venice1200/MiSTer_tty2oled/PCBs_and_Cases/tty2oled_esp32-DevKitC_board.png

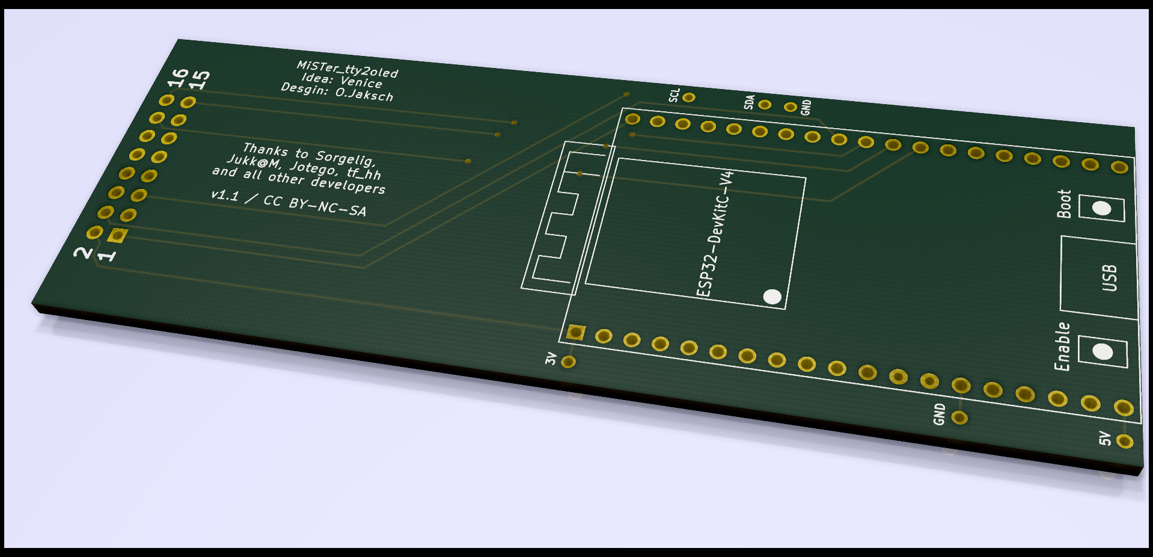
PCBs_and_Cases/tty2oled_esp32-DevKitC_board.png
