venice1200/MiSTer_tty2oled/PCBs_and_Cases/tty2oled_esp32-ttgo-t8-v1.7.1_board.png

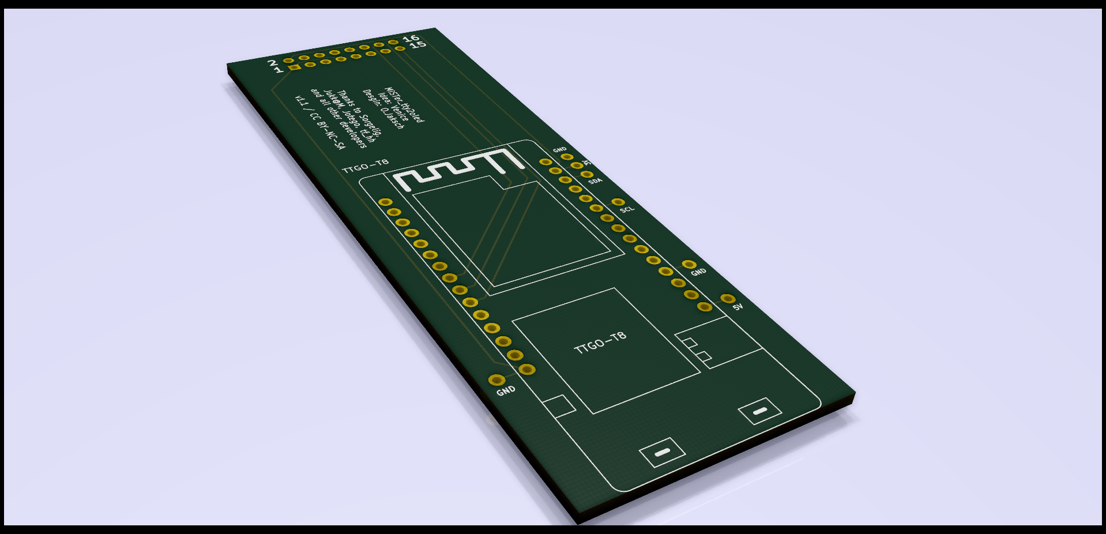
PCBs_and_Cases/tty2oled_esp32-ttgo-t8-v1.7.1_board.png
