venice1200/MiSTer_tty2oled/PCBs_and_Cases/tty2oled_esp8266-NodeMCU_v3_board.png

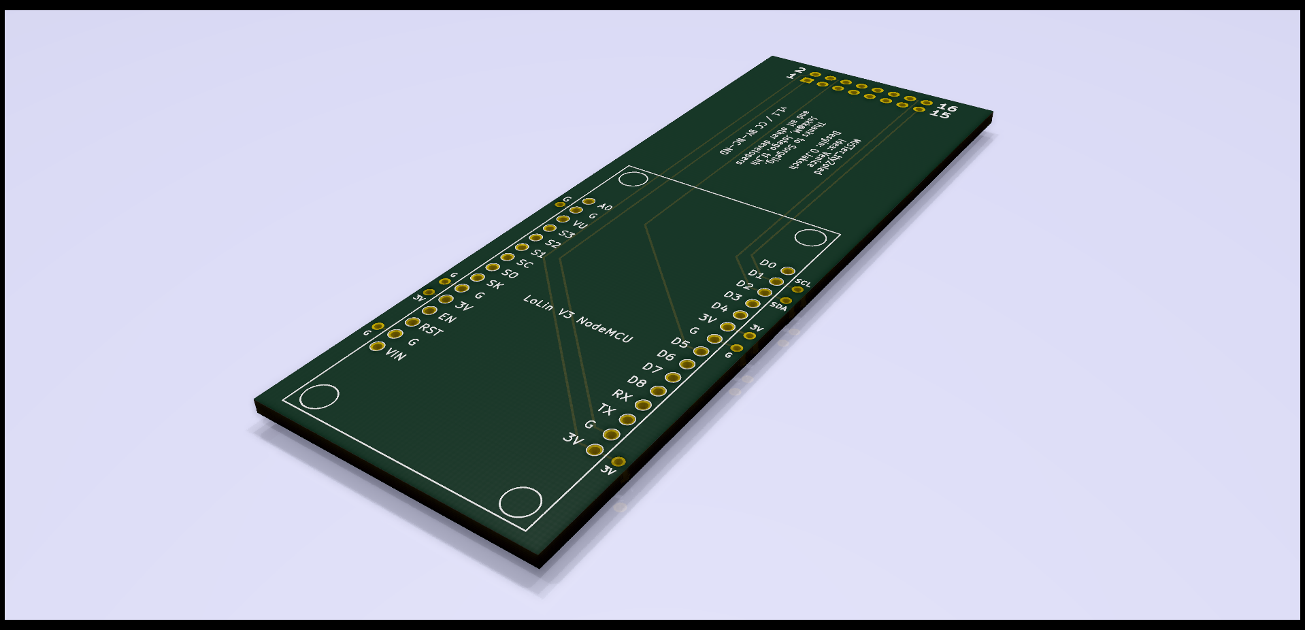
PCBs_and_Cases/tty2oled_esp8266-NodeMCU_v3_board.png
