venice1200/MiSTer_tty2oled/Pictures/altbeast55.jpg

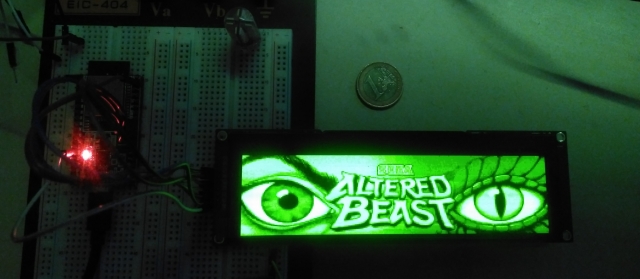
Pictures/altbeast55.jpg
