venice1200/MiSTer_tty2oled/Pictures/Arduino_1.8.13_ESP8266-NodeMCU_v3_Settings.png

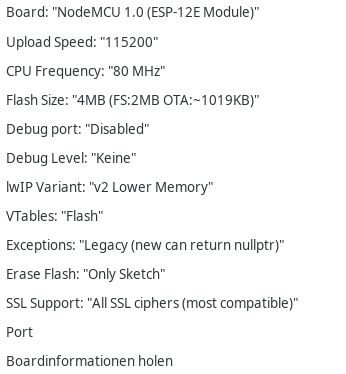
Pictures/Arduino_1.8.13_ESP8266-NodeMCU_v3_Settings.png
