venice1200/MiSTer_tty2oled/Pictures/Arduino_1.8.13_Lolin32_Settings.jpg

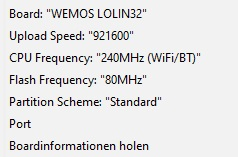
Pictures/Arduino_1.8.13_Lolin32_Settings.jpg
