venice1200/MiSTer_tty2oled/Pictures/Arduino_1.8.13_TTGO-T8_v1.7.1_Settings.jpg

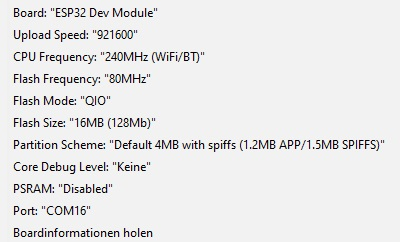
Pictures/Arduino_1.8.13_TTGO-T8_v1.7.1_Settings.jpg
