venice1200/MiSTer_tty2oled/Pictures/BasicOTA_small.jpg

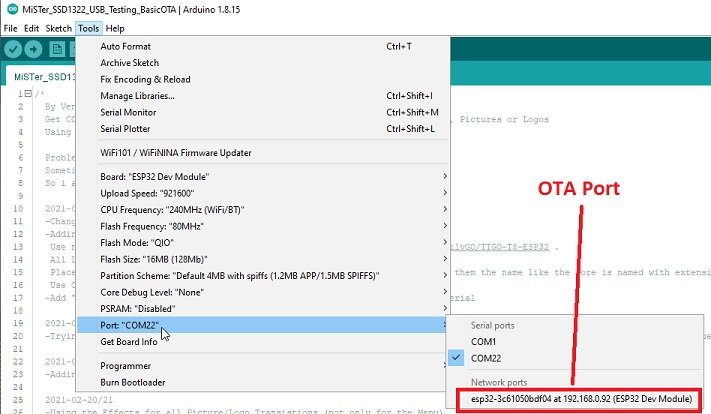
Pictures/BasicOTA_small.jpg
