venice1200/MiSTer_tty2oled/Pictures/Case_with_OLED_small.jpg

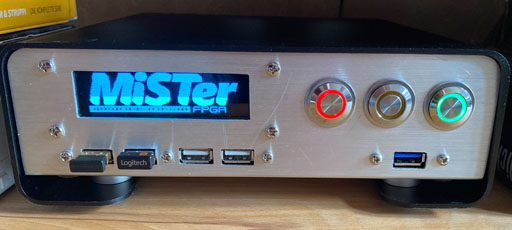
Pictures/Case_with_OLED_small.jpg
