venice1200/MiSTer_tty2oled/Pictures/Connection_Scheme_DevKitC_v4-SSD1322.jpg

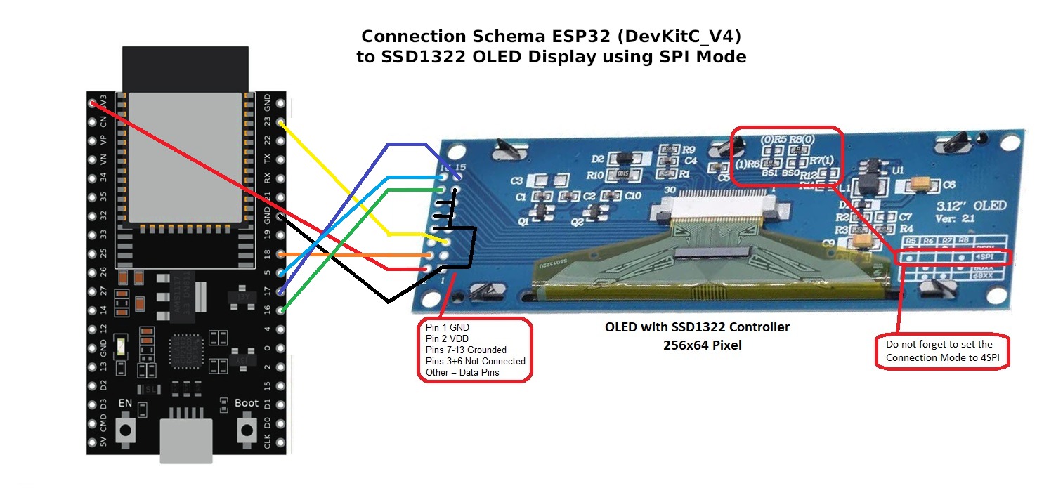
Pictures/Connection_Scheme_DevKitC_v4-SSD1322.jpg
