venice1200/MiSTer_tty2oled/Pictures/Connection_Scheme_NodeMCU-SSD1322.jpg

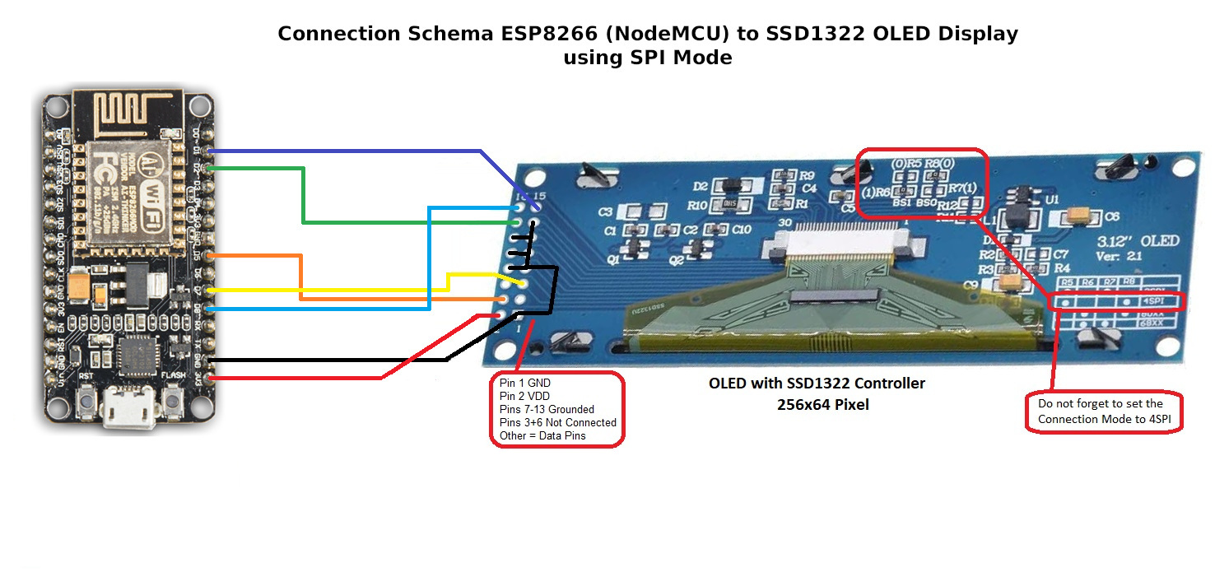
Pictures/Connection_Scheme_NodeMCU-SSD1322.jpg
