venice1200/MiSTer_tty2oled/Pictures/Connection_Scheme_NodeMCU-SSD1322_NewHaven_Displays.jpg.png

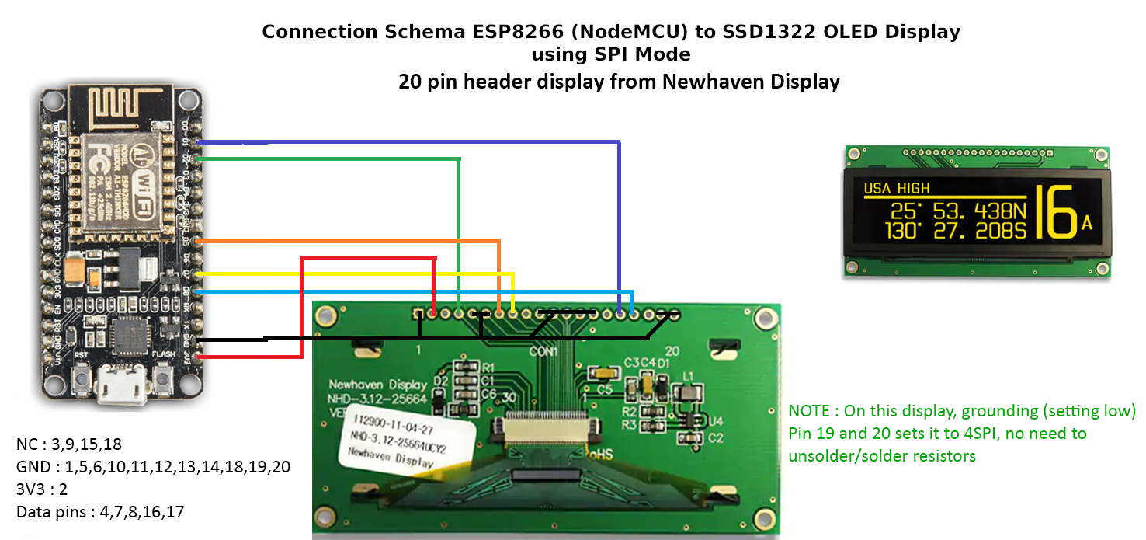
Pictures/Connection_Scheme_NodeMCU-SSD1322_NewHaven_Displays.jpg.png
