venice1200/MiSTer_tty2oled/Pictures/Connection_Scheme_TTGO-SSD1322.jpg

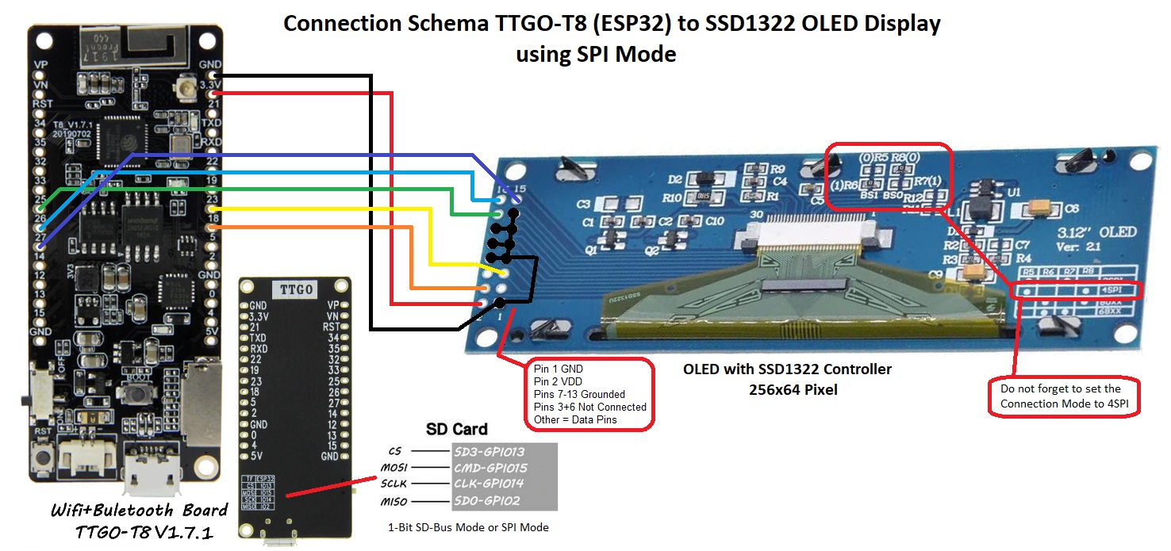
Pictures/Connection_Scheme_TTGO-SSD1322.jpg
