venice1200/MiSTer_tty2oled/Pictures/d.ti_rev1.2_small.jpg

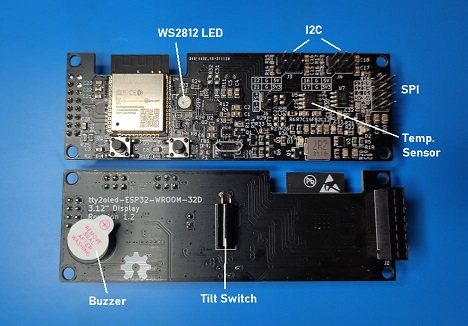
Pictures/d.ti_rev1.2_small.jpg
