venice1200/MiSTer_tty2oled/Pictures/d.ti_small.jpg

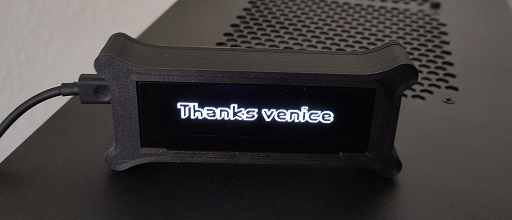
Pictures/d.ti_small.jpg
