venice1200/MiSTer_tty2oled/Pictures/d.ti_small_tty2oled_wroom_32d.jpg

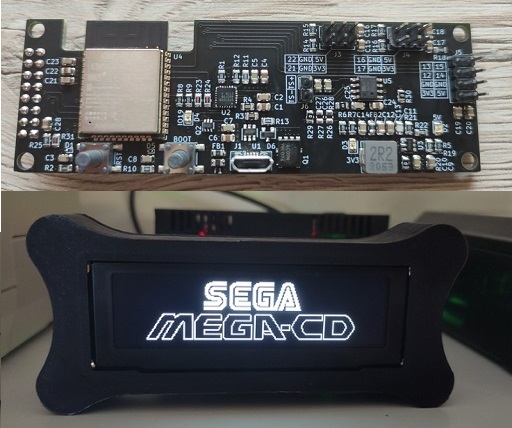
Pictures/d.ti_small_tty2oled_wroom_32d.jpg
