venice1200/MiSTer_tty2oled/Pictures/dave18_small.jpg

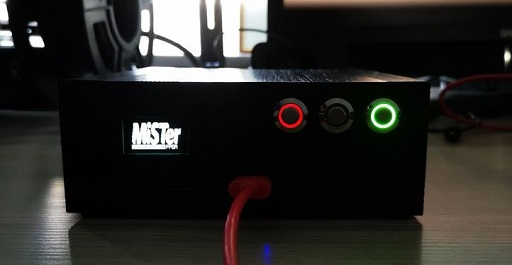
Pictures/dave18_small.jpg
