venice1200/MiSTer_tty2oled/Pictures/ExtCase312_small.jpg

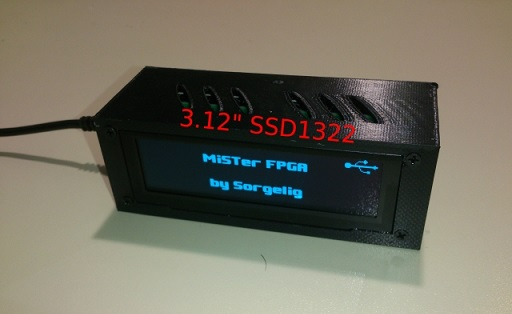
Pictures/ExtCase312_small.jpg
