venice1200/MiSTer_tty2oled/Pictures/gojira54_small.jpg

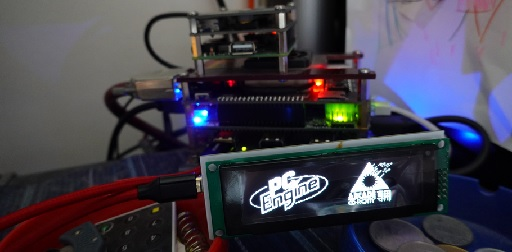
Pictures/gojira54_small.jpg
