venice1200/MiSTer_tty2oled/Pictures/jawler_small.jpg

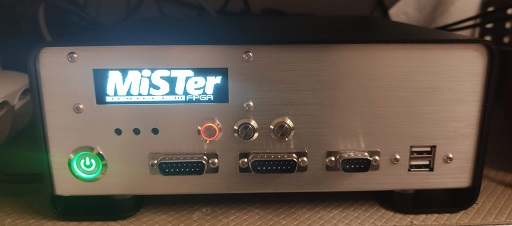
Pictures/jawler_small.jpg
