venice1200/MiSTer_tty2oled/Pictures/Jukk_at_M_small.jpg

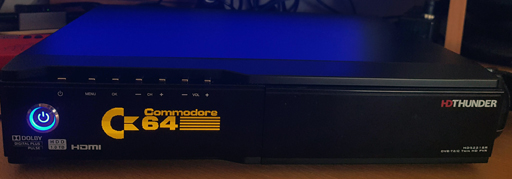
Pictures/Jukk_at_M_small.jpg
