venice1200/MiSTer_tty2oled/Pictures/Lolin_PCB_BOT_small.jpg

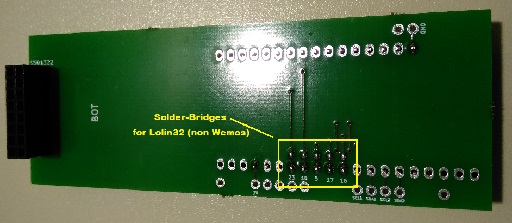
Pictures/Lolin_PCB_BOT_small.jpg
