venice1200/MiSTer_tty2oled/Pictures/Mellified_small.jpg

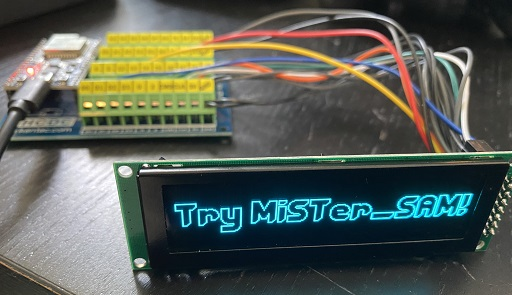
Pictures/Mellified_small.jpg
