venice1200/MiSTer_tty2oled/Pictures/OLED_Connection.jpg

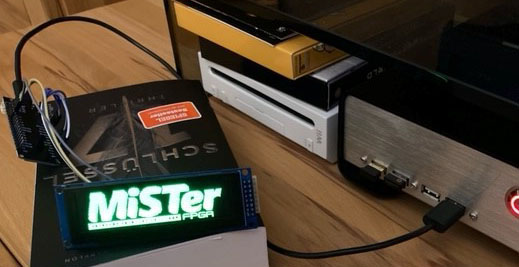
Pictures/OLED_Connection.jpg
