venice1200/MiSTer_tty2oled/Pictures/Prototype_small.jpg

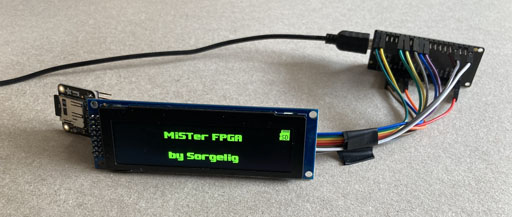
Pictures/Prototype_small.jpg
