venice1200/MiSTer_tty2oled/Pictures/rbz_couchcase_small.jpg

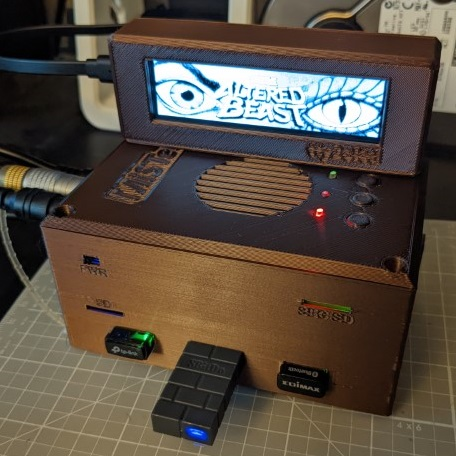
Pictures/rbz_couchcase_small.jpg
