venice1200/MiSTer_tty2oled/Pictures/Reg_small.JPG

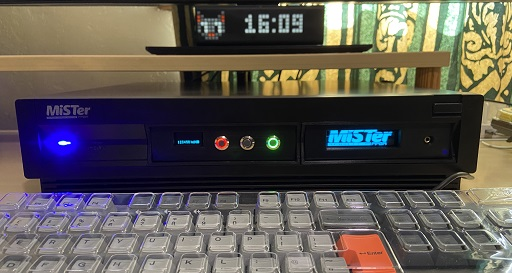
Pictures/Reg_small.JPG
