venice1200/MiSTer_tty2oled/Pictures/SerialMonitor_1.png

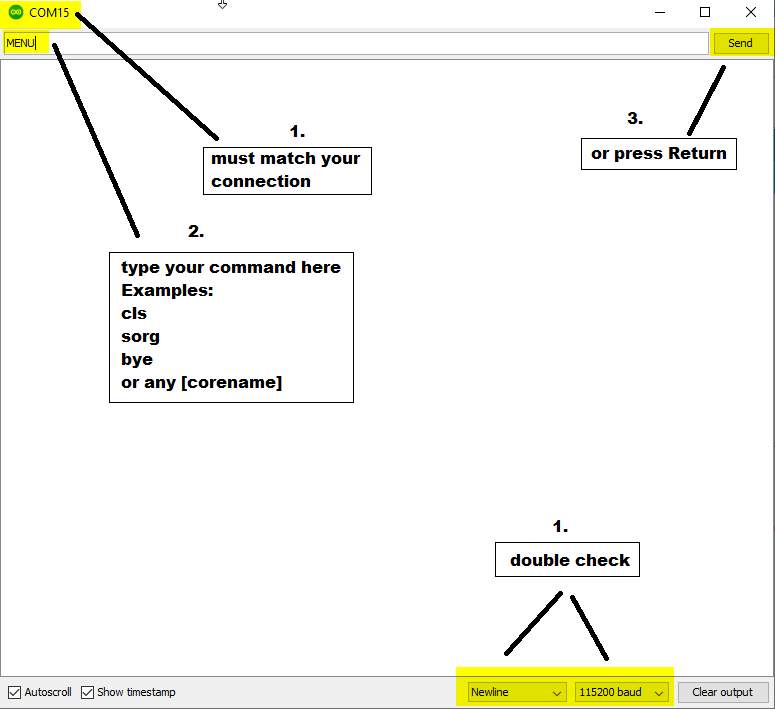
Pictures/SerialMonitor_1.png
