venice1200/MiSTer_tty2oled/Pictures/SerialMonitor_1_small.png

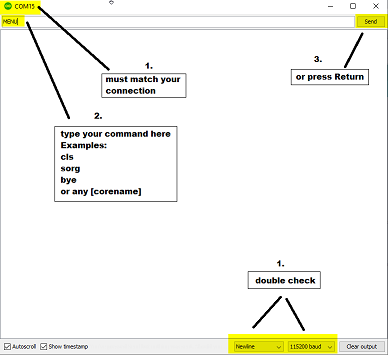
Pictures/SerialMonitor_1_small.png
