venice1200/MiSTer_tty2oled/Pictures/SerialMonitor_Open.png

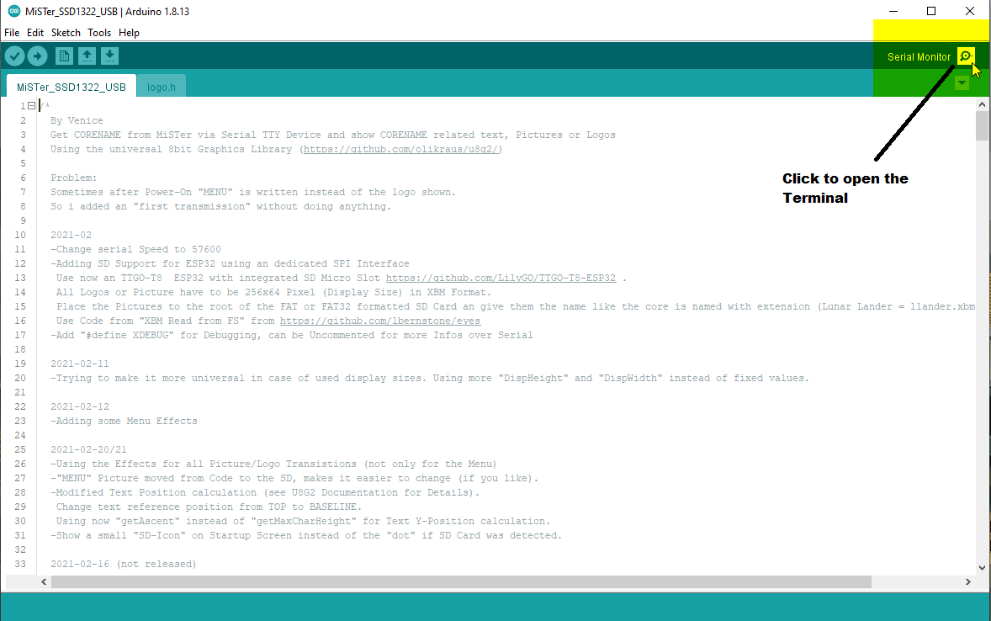
Pictures/SerialMonitor_Open.png
