venice1200/MiSTer_tty2oled/Pictures/stefer09-2_small.jpg

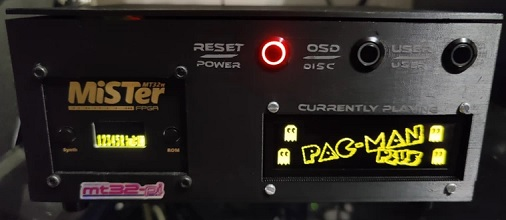
Pictures/stefer09-2_small.jpg
