venice1200/MiSTer_tty2oled/Pictures/stefer09_small.jpg

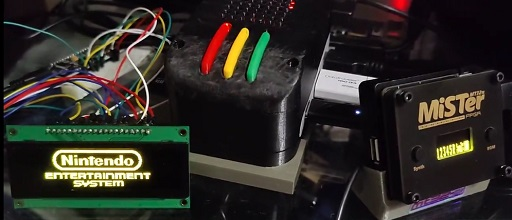
Pictures/stefer09_small.jpg
