venice1200/MiSTer_tty2oled/Pictures/ThreeColor_small.jpeg

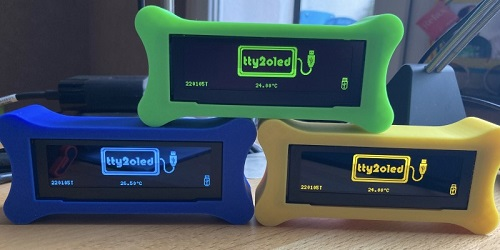
Pictures/ThreeColor_small.jpeg
