venice1200/MiSTer_tty2oled/Pictures/WiteWulf_small.jpg

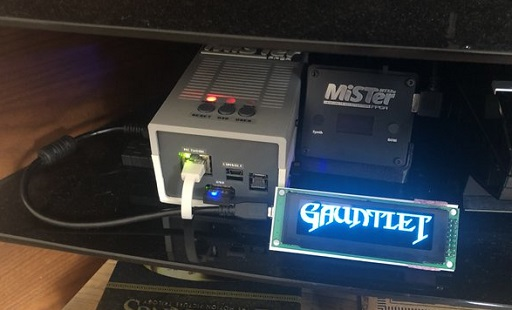
Pictures/WiteWulf_small.jpg
