venice1200/MiSTer_tty2oled/Pictures/With_OLED_Top_Small.jpg

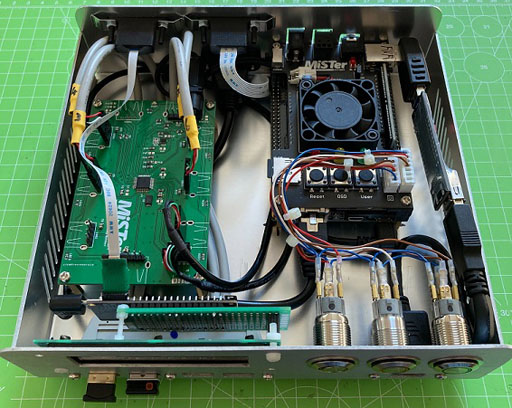
Pictures/With_OLED_Top_Small.jpg
