venice1200/MiSTer_tty2oled/Pictures/HowTo/tty2oled_arduino_01_folders.png

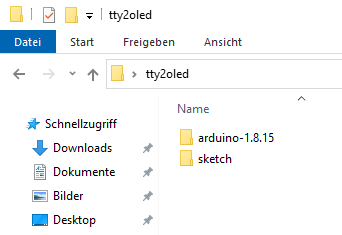
Pictures/HowTo/tty2oled_arduino_01_folders.png
