venice1200/MiSTer_tty2oled/Pictures/HowTo/tty2oled_arduino_02_preferences.png

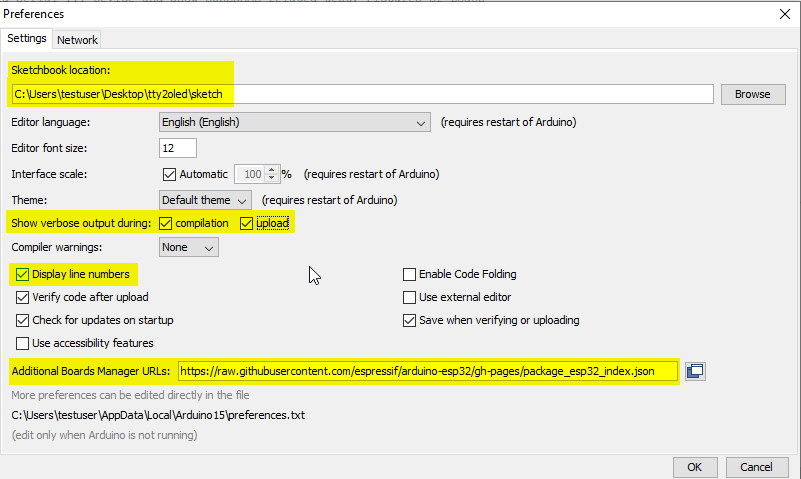
Pictures/HowTo/tty2oled_arduino_02_preferences.png
