venice1200/MiSTer_tty2oled/Pictures/HowTo/tty2oled_arduino_03_board_01_menu.png

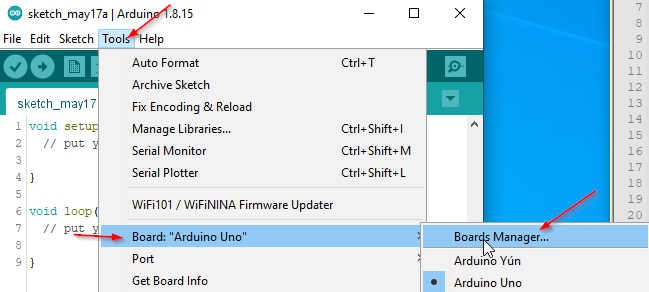
Pictures/HowTo/tty2oled_arduino_03_board_01_menu.png
