venice1200/MiSTer_tty2oled/Pictures/HowTo/tty2oled_arduino_04_library_02_u8g2.png

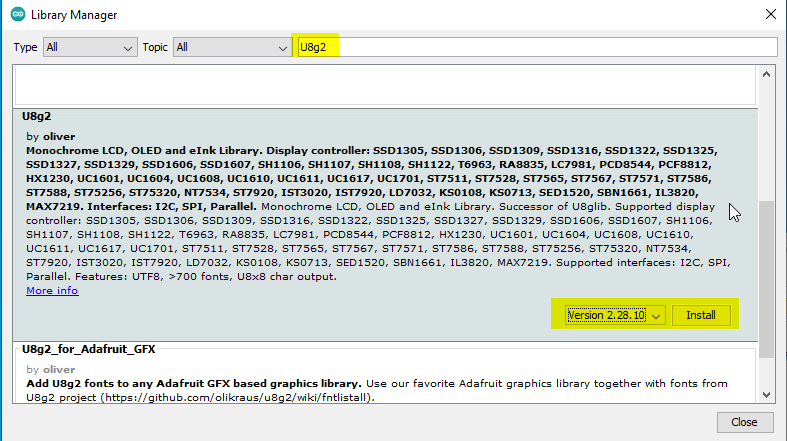
Pictures/HowTo/tty2oled_arduino_04_library_02_u8g2.png
