venice1200/MiSTer_tty2oled/Pictures/HowTo/tty2oled_arduino_06_sketch_01_open.png

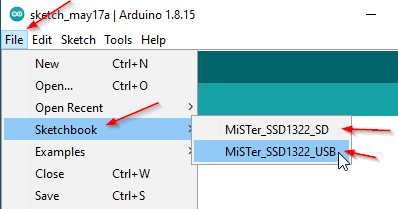
Pictures/HowTo/tty2oled_arduino_06_sketch_01_open.png
