venice1200/MiSTer_tty2oled/Pictures/HowTo/tty2oled_arduino_06_sketch_02_opened.png

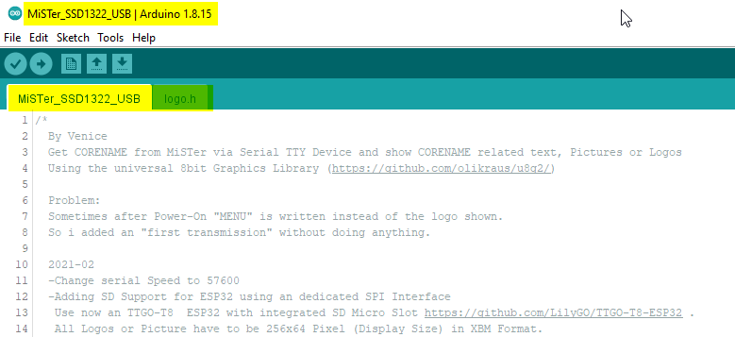
Pictures/HowTo/tty2oled_arduino_06_sketch_02_opened.png
