venice1200/MiSTer_tty2oled/Pictures/HowTo/tty2oled_arduino_08_sketch_01_choose_ESP.png

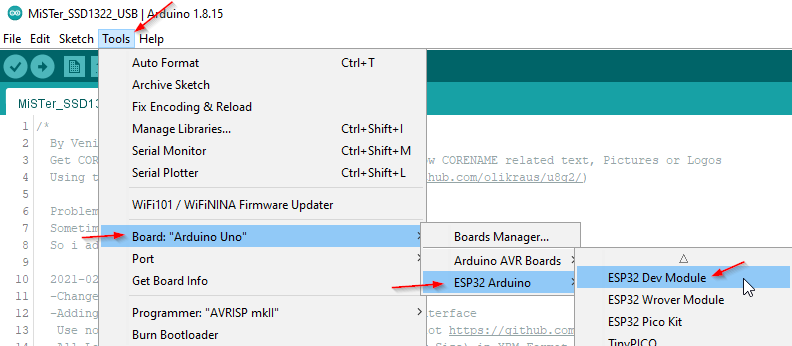
Pictures/HowTo/tty2oled_arduino_08_sketch_01_choose_ESP.png
