venice1200/MiSTer_tty2oled/Pictures/HowTo/tty2oled_arduino_08_sketch_02_check_ESP.png

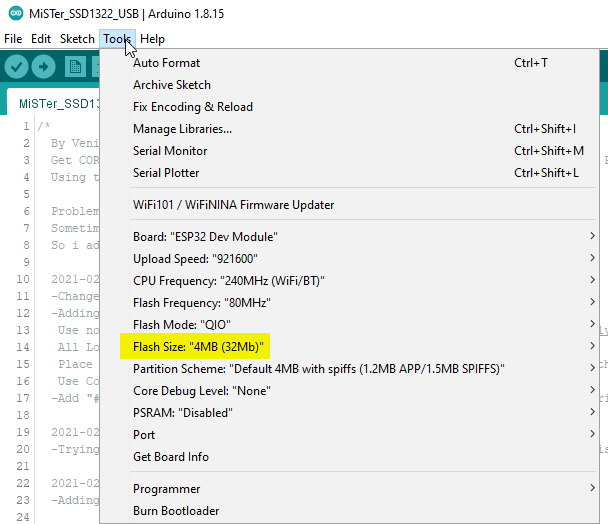
Pictures/HowTo/tty2oled_arduino_08_sketch_02_check_ESP.png
