venice1200/MiSTer_tty2oled/Pictures/HowTo/tty2oled_arduino_09_sketch_02_compiling.png

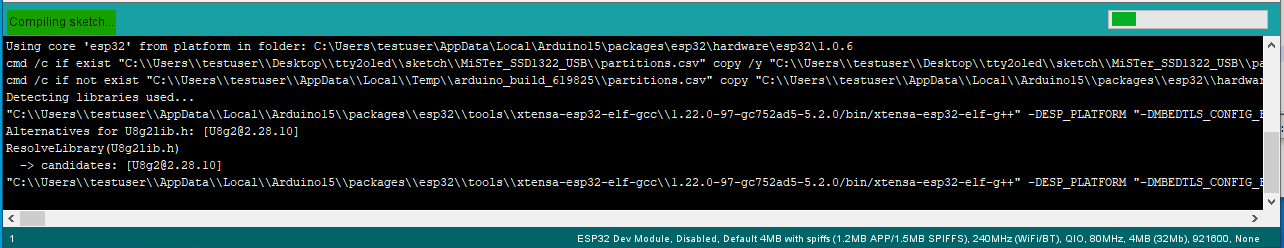
Pictures/HowTo/tty2oled_arduino_09_sketch_02_compiling.png
