venice1200/MiSTer_tty2oled/Pictures/HowTo/tty2oled_arduino_09_sketch_03_compiled.png

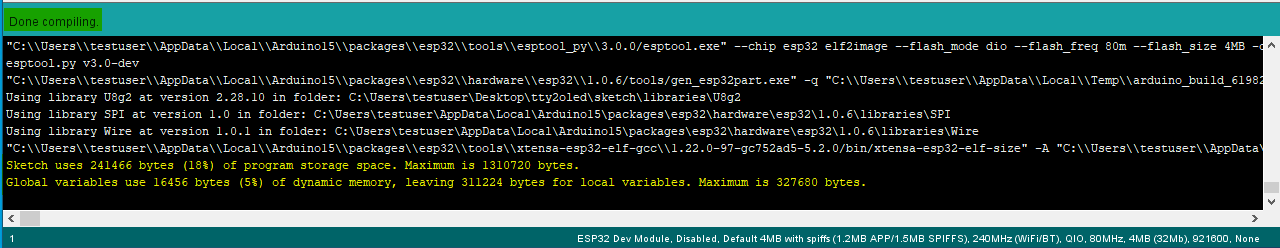
Pictures/HowTo/tty2oled_arduino_09_sketch_03_compiled.png
