venice1200/MiSTer_tty2oled/Pictures/HowTo/tty2oled_arduino_10_windows_02_driver.png

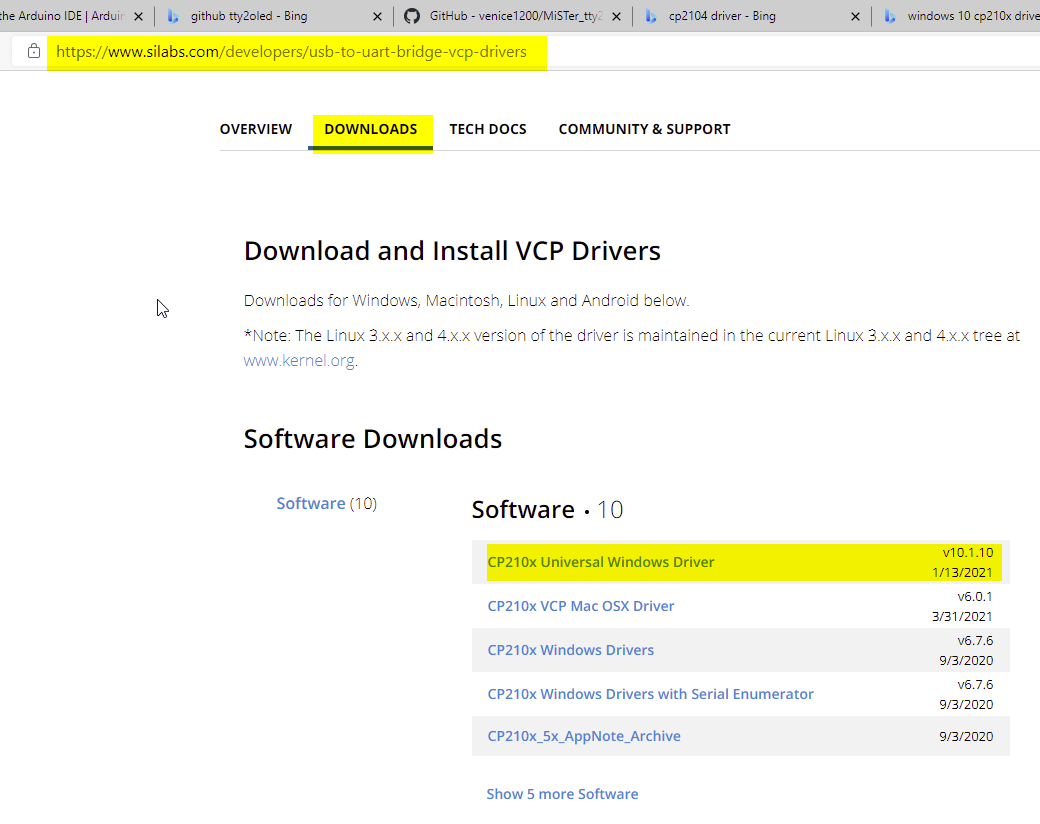
Pictures/HowTo/tty2oled_arduino_10_windows_02_driver.png
