venice1200/MiSTer_tty2oled/Pictures/HowTo/tty2oled_arduino_11_sketch_01_port.png

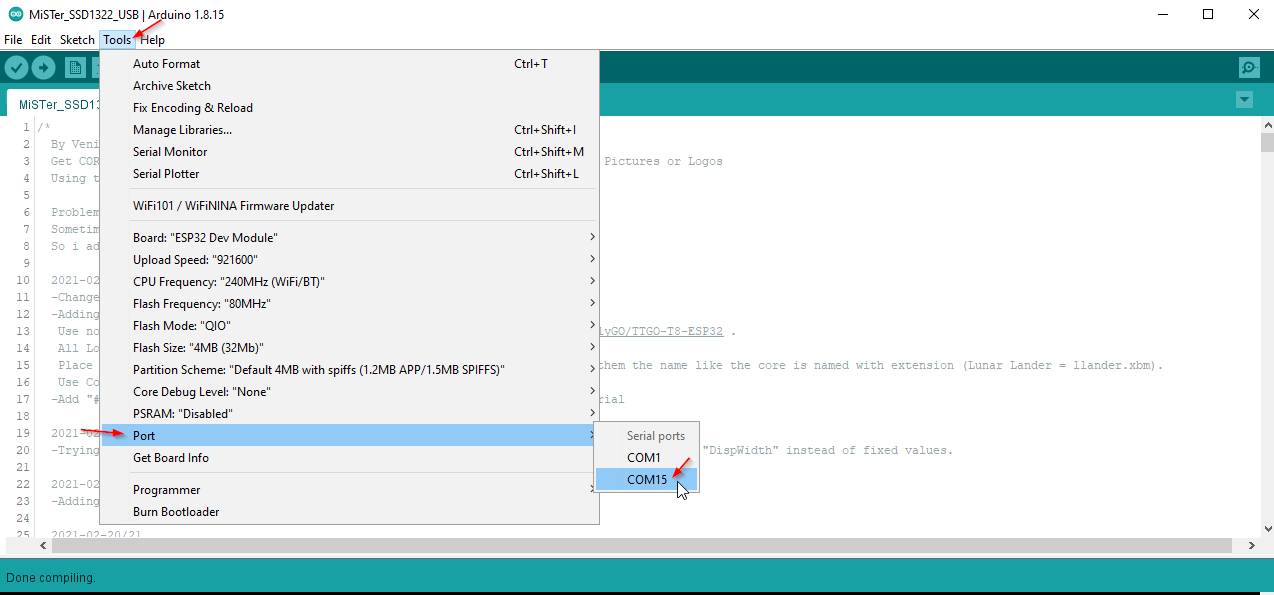
Pictures/HowTo/tty2oled_arduino_11_sketch_01_port.png
