venice1200/MiSTer_tty2oled/Pictures/HowTo/tty2oled_arduino_12_sketch_01_upload.png

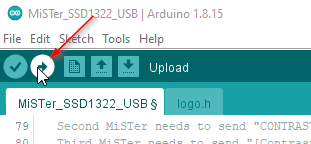
Pictures/HowTo/tty2oled_arduino_12_sketch_01_upload.png
