venice1200/MiSTer_tty2oled/Pictures/HowTo/tty2oled_arduino_12_sketch_02_uploading.png

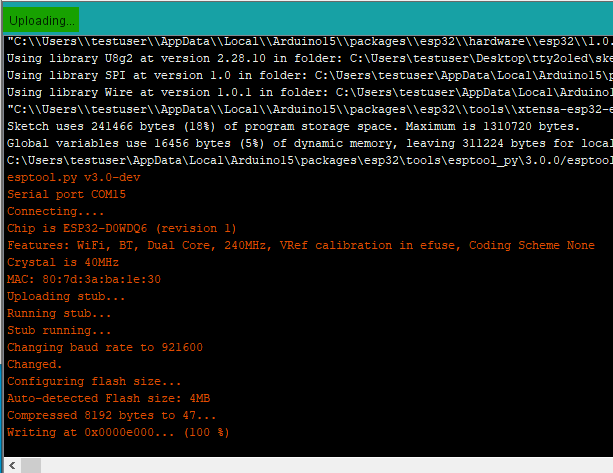
Pictures/HowTo/tty2oled_arduino_12_sketch_02_uploading.png
