venice1200/MiSTer_tty2oled/Pictures/HowTo/tty2oled_arduino_14_BasicOTA_06.jpg

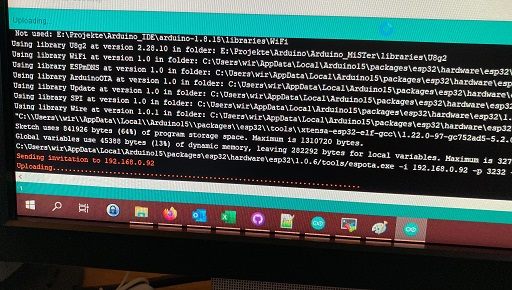
Pictures/HowTo/tty2oled_arduino_14_BasicOTA_06.jpg
