venice1200/MiSTer_tty2oled/Pictures/312_v21_measured.jpg

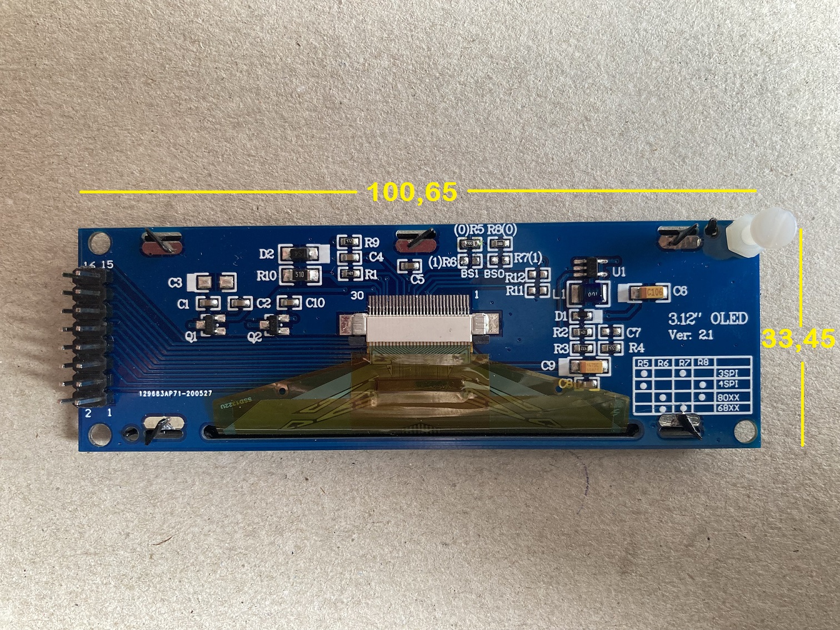
Pictures/312_v21_measured.jpg
