venice1200/MiSTer_tty2oled/MiSTer_SSD1322_USB/logo.h

/*
  Logo's for MiSTer in XMB Format
  Most of them defined as "static const unsigned char <Name>[]U8X8_PROGMEM" for the useage of "u8g2.drawXBMP"
  only the mister logo is defined as "static unsigned char <Name>[]" because the effects must use "u8g2.drawXBM".
*/

/* Menu Picture moved to SD */

/* -------------------- U8X8_PROGMEM -----------------------*/

// SD Logo 16x16
#define sdcard_icon16_width 16
#define sdcard_icon16_height 16
const uint8_t PROGMEM sdcard_icon16[] = {
 0x50,0x55,0x58,0x55,0x58,0x55,0x58,0x55,0xf8,0x7f,0xfc,0x7f,0xfe,0x7f,0xfe,
 0x7f,0x1e,0x71,0xec,0x6d,0xec,0x6d,0x9e,0x6d,0x7e,0x6d,0x7e,0x6d,0x8e,0x71,
 0xfe,0x7f };

#define usb_icon_width 9
#define usb_icon_height 18
const uint8_t PROGMEM usb_icon[] = {
 0xfe,0x00,0x82,0x00,0xaa,0x00,0xaa,0x00,0x82,0x00,0xff,0x01,
 0x01,0x01,0x11,0x01,0x51,0x01,0x55,0x01,0x35,0x01,0x19,0x01,
 0x11,0x01,0x11,0x01,0x01,0x01,0x39,0x01,0x82,0x00,0x7c,0x00};

// Sorgelig's Icon 16x16
#define sorgelig_icon16_width 16
#define sorgelig_icon16_height 16
const uint8_t PROGMEM sorgelig_icon16[] = {
 0x38,0x1c,0x38,0x1c,0xfc,0x3f,0xfe,0x7f,0x06,0x60,0xc6,0x61,0xfe,0x7f,0xfe,
 0x7f,0xdf,0xfb,0xfb,0xdf,0xe3,0xc7,0x26,0x64,0x06,0x60,0x86,0x61,0xc2,0xc3,
 0x7e,0x7f };
 
// MiSTer Logo for Screensaver
#define mister_logo32_width 116
#define mister_logo32_height 32
const uint8_t PROGMEM mister_logo32[] = {
   0x00, 0x00, 0x00, 0x00, 0xc0, 0x1f, 0xe0, 0x1f, 0x00, 0x00, 0x00, 0x00,
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
 0x00,0x00,0x00,0x00,0x00,0x00,0x00,0x00,0x00,0x00,0x00,0x00,
 0x55,0x55,0x55,0x55,0x00,0x00,0x00,0x10,0x00,0x00,0x00,0x00,
 0x00,0x00,0x00,0x00,0x00,0x00,0x00,0x00,0x00,0x00,0x00,0x00,
 0x00,0x00,0x00,0x00,0x00,0x00,0x00,0x00,0xAB,0xAA,0xAA,0xAA,
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
