venice1200/MiSTer_tty2oled/Testing/docs_and_obsoletes/esptool.py

#!/usr/bin/python3
#
# ESP8266 & ESP32 family & ESP8684 ROM Bootloader Utility
# Copyright (C) 2014-2021 Fredrik Ahlberg, Angus Gratton, Espressif Systems (Shanghai) CO LTD, other contributors as noted.
# https://github.com/espressif/esptool
#
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
from __future__ import division, print_function

import argparse
import base64
import binascii
import copy
import hashlib
import inspect
import io
import itertools
import os
import re
import shlex
import string
import struct
import sys
import time
import zlib

try:
    import serial
except ImportError:
    print("Pyserial is not installed for %s. Check the README for installation instructions." % (sys.executable))
    raise

# check 'serial' is 'pyserial' and not 'serial' https://github.com/espressif/esptool/issues/269
try:
    if "serialization" in serial.__doc__ and "deserialization" in serial.__doc__:
        raise ImportError("""
esptool.py depends on pyserial, but there is a conflict with a currently installed package named 'serial'.

You may be able to work around this by 'pip uninstall serial; pip install pyserial' \
but this may break other installed Python software that depends on 'serial'.

There is no good fix for this right now, apart from configuring virtualenvs. \
See https://github.com/espressif/esptool/issues/269#issuecomment-385298196 for discussion of the underlying issue(s).""")
except TypeError:
    pass  # __doc__ returns None for pyserial

try:
    import serial.tools.list_ports as list_ports
except ImportError:
    print("The installed version (%s) of pyserial appears to be too old for esptool.py (Python interpreter %s). "
          "Check the README for installation instructions." % (sys.VERSION, sys.executable))
    raise
except Exception:
    if sys.platform == "darwin":
        # swallow the exception, this is a known issue in pyserial+macOS Big Sur preview ref https://github.com/espressif/esptool/issues/540
        list_ports = None
    else:
        raise


__version__ = "3.2"

MAX_UINT32 = 0xffffffff
MAX_UINT24 = 0xffffff

DEFAULT_TIMEOUT = 3                   # timeout for most flash operations
START_FLASH_TIMEOUT = 20              # timeout for starting flash (may perform erase)
CHIP_ERASE_TIMEOUT = 120              # timeout for full chip erase
MAX_TIMEOUT = CHIP_ERASE_TIMEOUT * 2  # longest any command can run
SYNC_TIMEOUT = 0.1                    # timeout for syncing with bootloader
MD5_TIMEOUT_PER_MB = 8                # timeout (per megabyte) for calculating md5sum
ERASE_REGION_TIMEOUT_PER_MB = 30      # timeout (per megabyte) for erasing a region
ERASE_WRITE_TIMEOUT_PER_MB = 40       # timeout (per megabyte) for erasing and writing data
MEM_END_ROM_TIMEOUT = 0.05            # special short timeout for ESP_MEM_END, as it may never respond
DEFAULT_SERIAL_WRITE_TIMEOUT = 10     # timeout for serial port write
DEFAULT_CONNECT_ATTEMPTS = 7          # default number of times to try connection

SUPPORTED_CHIPS = ['esp8266', 'esp32', 'esp32s2', 'esp32s3beta2', 'esp32s3', 'esp32c3', 'esp32c6beta', 'esp32h2', 'esp8684']


def timeout_per_mb(seconds_per_mb, size_bytes):
    """ Scales timeouts which are size-specific """
    result = seconds_per_mb * (size_bytes / 1e6)
    if result < DEFAULT_TIMEOUT:
        return DEFAULT_TIMEOUT
    return result


def _chip_to_rom_loader(chip):
    return {
        'esp8266': ESP8266ROM,
        'esp32': ESP32ROM,
        'esp32s2': ESP32S2ROM,
        'esp32s3beta2': ESP32S3BETA2ROM,
        'esp32s3': ESP32S3ROM,
        'esp32c3': ESP32C3ROM,
        'esp32c6beta': ESP32C6BETAROM,
        'esp32h2': ESP32H2ROM,
        'esp8684': ESP8684ROM,
    }[chip]


def get_default_connected_device(serial_list, port, connect_attempts, initial_baud, chip='auto', trace=False,
                                 before='default_reset'):
    _esp = None
    for each_port in reversed(serial_list):
        print("Serial port %s" % each_port)
        try:
            if chip == 'auto':
                _esp = ESPLoader.detect_chip(each_port, initial_baud, before, trace,
                                             connect_attempts)
            else:
                chip_class = _chip_to_rom_loader(chip)
                _esp = chip_class(each_port, initial_baud, trace)
                _esp.connect(before, connect_attempts)
            break
        except (FatalError, OSError) as err:
            if port is not None:
                raise
            print("%s failed to connect: %s" % (each_port, err))
            _esp = None
    return _esp


DETECTED_FLASH_SIZES = {0x12: '256KB', 0x13: '512KB', 0x14: '1MB',
                        0x15: '2MB', 0x16: '4MB', 0x17: '8MB',
                        0x18: '16MB', 0x19: '32MB', 0x1a: '64MB'}


def check_supported_function(func, check_func):
    """
    Decorator implementation that wraps a check around an ESPLoader
    bootloader function to check if it's supported.

    This is used to capture the multidimensional differences in
    functionality between the ESP8266 & ESP32/32S2/32S3/32C3 & ESP8684 ROM loaders, and the
    software stub that runs on both. Not possible to do this cleanly
    via inheritance alone.
    """
    def inner(*args, **kwargs):
        obj = args[0]
        if check_func(obj):
            return func(*args, **kwargs)
        else:
            raise NotImplementedInROMError(obj, func)
    return inner


def stub_function_only(func):
    """ Attribute for a function only supported in the software stub loader """
    return check_supported_function(func, lambda o: o.IS_STUB)


def stub_and_esp32_function_only(func):
    """ Attribute for a function only supported by software stubs or ESP32/32S2/32S3/32C3 ROM """
    return check_supported_function(func, lambda o: o.IS_STUB or isinstance(o, ESP32ROM))


def esp32s3_or_newer_function_only(func):
    """ Attribute for a function only supported by ESP32S3/32C3 & ESP8684 ROM """
    return check_supported_function(func, lambda o: isinstance(o, ESP32S3ROM) or isinstance(o, ESP32C3ROM))


PYTHON2 = sys.version_info[0] < 3  # True if on pre-Python 3

# Function to return nth byte of a bitstring
# Different behaviour on Python 2 vs 3
if PYTHON2:
    def byte(bitstr, index):
        return ord(bitstr[index])
else:
    def byte(bitstr, index):
        return bitstr[index]

# Provide a 'basestring' class on Python 3
try:
    basestring
except NameError:
    basestring = str


def print_overwrite(message, last_line=False):
    """ Print a message, overwriting the currently printed line.

    If last_line is False, don't append a newline at the end (expecting another subsequent call will overwrite this one.)

    After a sequence of calls with last_line=False, call once with last_line=True.

    If output is not a TTY (for example redirected a pipe), no overwriting happens and this function is the same as print().
    """
    if sys.stdout.isatty():
        print("\r%s" % message, end='\n' if last_line else '')
    else:
        print(message)


def _mask_to_shift(mask):
    """ Return the index of the least significant bit in the mask """
    shift = 0
    while mask & 0x1 == 0:
        shift += 1
        mask >>= 1
    return shift


def esp8266_function_only(func):
    """ Attribute for a function only supported on ESP8266 """
    return check_supported_function(func, lambda o: o.CHIP_NAME == "ESP8266")


class ESPLoader(object):
    """ Base class providing access to ESP ROM & software stub bootloaders.
    Subclasses provide ESP8266 & ESP32 Family & ESP8684 specific functionality.

    Don't instantiate this base class directly, either instantiate a subclass or
    call ESPLoader.detect_chip() which will interrogate the chip and return the
    appropriate subclass instance.

    """
    CHIP_NAME = "Espressif device"
    IS_STUB = False

    FPGA_SLOW_BOOT = False

    DEFAULT_PORT = "/dev/ttyUSB0"

    # Commands supported by ESP8266 ROM bootloader
    ESP_FLASH_BEGIN = 0x02
    ESP_FLASH_DATA  = 0x03
    ESP_FLASH_END   = 0x04
    ESP_MEM_BEGIN   = 0x05
    ESP_MEM_END     = 0x06
    ESP_MEM_DATA    = 0x07
    ESP_SYNC        = 0x08
    ESP_WRITE_REG   = 0x09
    ESP_READ_REG    = 0x0a

    # Some comands supported by ESP32 & ESP8684 ROM bootloader (or -8266 w/ stub)
    ESP_SPI_SET_PARAMS = 0x0B
    ESP_SPI_ATTACH     = 0x0D
    ESP_READ_FLASH_SLOW  = 0x0e  # ROM only, much slower than the stub flash read
    ESP_CHANGE_BAUDRATE = 0x0F
    ESP_FLASH_DEFL_BEGIN = 0x10
    ESP_FLASH_DEFL_DATA  = 0x11
    ESP_FLASH_DEFL_END   = 0x12
    ESP_SPI_FLASH_MD5    = 0x13

    # Commands supported by ESP32-S2/S3/C3/C6 & ESP8684 ROM bootloader only
    ESP_GET_SECURITY_INFO = 0x14

    # Some commands supported by stub only
    ESP_ERASE_FLASH = 0xD0
    ESP_ERASE_REGION = 0xD1
    ESP_READ_FLASH = 0xD2
    ESP_RUN_USER_CODE = 0xD3

    # Flash encryption encrypted data command
    ESP_FLASH_ENCRYPT_DATA = 0xD4

    # Response code(s) sent by ROM
    ROM_INVALID_RECV_MSG = 0x05   # response if an invalid message is received

    # Maximum block sized for RAM and Flash writes, respectively.
    ESP_RAM_BLOCK   = 0x1800

    FLASH_WRITE_SIZE = 0x400

    # Default baudrate. The ROM auto-bauds, so we can use more or less whatever we want.
    ESP_ROM_BAUD    = 115200

    # First byte of the application image
    ESP_IMAGE_MAGIC = 0xe9

    # Initial state for the checksum routine
    ESP_CHECKSUM_MAGIC = 0xef

    # Flash sector size, minimum unit of erase.
    FLASH_SECTOR_SIZE = 0x1000

    UART_DATE_REG_ADDR = 0x60000078

    CHIP_DETECT_MAGIC_REG_ADDR = 0x40001000  # This ROM address has a different value on each chip model

    UART_CLKDIV_MASK = 0xFFFFF

    # Memory addresses
    IROM_MAP_START = 0x40200000
    IROM_MAP_END = 0x40300000

    # The number of bytes in the UART response that signify command status
    STATUS_BYTES_LENGTH = 2

    # Response to ESP_SYNC might indicate that flasher stub is running instead of the ROM bootloader
    sync_stub_detected = False

    # Device PIDs
    USB_JTAG_SERIAL_PID = 0x1001

    # Chip IDs that are no longer supported by esptool
    UNSUPPORTED_CHIPS = {6: "ESP32-S3(beta 3)"}

    def __init__(self, port=DEFAULT_PORT, baud=ESP_ROM_BAUD, trace_enabled=False):
        """Base constructor for ESPLoader bootloader interaction

        Don't call this constructor, either instantiate ESP8266ROM
        or ESP32ROM, or use ESPLoader.detect_chip().

        This base class has all of the instance methods for bootloader
        functionality supported across various chips & stub
        loaders. Subclasses replace the functions they don't support
        with ones which throw NotImplementedInROMError().

        """
        self.secure_download_mode = False  # flag is set to True if esptool detects the ROM is in Secure Download Mode
        self.stub_is_disabled = False  # flag is set to True if esptool detects conditions which require the stub to be disabled

        if isinstance(port, basestring):
            self._port = serial.serial_for_url(port)
        else:
            self._port = port
        self._slip_reader = slip_reader(self._port, self.trace)
        # setting baud rate in a separate step is a workaround for
        # CH341 driver on some Linux versions (this opens at 9600 then
        # sets), shouldn't matter for other platforms/drivers. See
        # https://github.com/espressif/esptool/issues/44#issuecomment-107094446
        self._set_port_baudrate(baud)
        self._trace_enabled = trace_enabled
        # set write timeout, to prevent esptool blocked at write forever.
        try:
            self._port.write_timeout = DEFAULT_SERIAL_WRITE_TIMEOUT
        except NotImplementedError:
            # no write timeout for RFC2217 ports
            # need to set the property back to None or it will continue to fail
            self._port.write_timeout = None

    @property
    def serial_port(self):
        return self._port.port

    def _set_port_baudrate(self, baud):
        try:
            self._port.baudrate = baud
        except IOError:
            raise FatalError("Failed to set baud rate %d. The driver may not support this rate." % baud)

    @staticmethod
    def detect_chip(port=DEFAULT_PORT, baud=ESP_ROM_BAUD, connect_mode='default_reset', trace_enabled=False,
                    connect_attempts=DEFAULT_CONNECT_ATTEMPTS):
        """ Use serial access to detect the chip type.

        First, get_security_info command is sent to detect the ID of the chip
        (supported only by ESP32-C3 and later, works even in the Secure Download Mode).
        If this fails, we reconnect and fall-back to reading the magic number.
        It's mapped at a specific ROM address and has a different value on each chip model.
        This way we can use one memory read and compare it to the magic number for each chip type.

        This routine automatically performs ESPLoader.connect() (passing
        connect_mode parameter) as part of querying the chip.
        """
        inst = None
        detect_port = ESPLoader(port, baud, trace_enabled=trace_enabled)
        detect_port.connect(connect_mode, connect_attempts, detecting=True)
        try:
            print('Detecting chip type...', end='')
            res = detect_port.check_command('get security info', ESPLoader.ESP_GET_SECURITY_INFO, b'')
            res = struct.unpack("<IBBBBBBBBI", res[:16])  # 4b flags, 1b flash_crypt_cnt, 7*1b key_purposes, 4b chip_id
            chip_id = res[9]  # 2/4 status bytes invariant

            for cls in [ESP32S3BETA2ROM, ESP32S3ROM, ESP32C3ROM, ESP32C6BETAROM, ESP32H2ROM, ESP8684ROM]:
                if chip_id == cls.IMAGE_CHIP_ID:
                    inst = cls(detect_port._port, baud, trace_enabled=trace_enabled)
                    inst._post_connect()
        except (UnsupportedCommandError, struct.error, FatalError):
            # UnsupportedCmdErr: ESP8266, ESP32 ROM | struct.err: ESP32S2 | FatalErr: ESP8266, ESP32 STUB
            print(" Unsupported detection protocol, switching and trying again...")
            try:
                detect_port.connect(connect_mode, connect_attempts, detecting=True, warnings=False)  # Need to connect again
                print('Detecting chip type...', end='')
                sys.stdout.flush()
                chip_magic_value = detect_port.read_reg(ESPLoader.CHIP_DETECT_MAGIC_REG_ADDR)

                for cls in [ESP8266ROM, ESP32ROM, ESP32S2ROM, ESP32S3BETA2ROM, ESP32S3ROM, ESP32C3ROM, ESP32C6BETAROM, ESP32H2ROM, ESP8684ROM]:
                    if chip_magic_value in cls.CHIP_DETECT_MAGIC_VALUE:
                        inst = cls(detect_port._port, baud, trace_enabled=trace_enabled)
                        inst._post_connect()
                        inst.check_chip_id()
            except UnsupportedCommandError:
                raise FatalError("Unsupported Command Error received. Probably this means Secure Download Mode is enabled, "
                                 "autodetection will not work. Need to manually specify the chip.")
        finally:
            if inst is not None:
                print(' %s' % inst.CHIP_NAME, end='')
                if detect_port.sync_stub_detected:
                    inst = inst.STUB_CLASS(inst)
                    inst.sync_stub_detected = True
                print('')  # end line
                return inst
        raise FatalError("Unexpected CHIP magic value 0x%08x. Failed to autodetect chip type." % (chip_magic_value))

    """ Read a SLIP packet from the serial port """
    def read(self):
        return next(self._slip_reader)

    """ Write bytes to the serial port while performing SLIP escaping """
    def write(self, packet):
        buf = b'\xc0' \
              + (packet.replace(b'\xdb', b'\xdb\xdd').replace(b'\xc0', b'\xdb\xdc')) \
              + b'\xc0'
        self.trace("Write %d bytes: %s", len(buf), HexFormatter(buf))
        self._port.write(buf)

    def trace(self, message, *format_args):
        if self._trace_enabled:
            now = time.time()
            try:

                delta = now - self._last_trace
            except AttributeError:
                delta = 0.0
            self._last_trace = now
            prefix = "TRACE +%.3f " % delta
            print(prefix + (message % format_args))

    """ Calculate checksum of a blob, as it is defined by the ROM """
    @staticmethod
    def checksum(data, state=ESP_CHECKSUM_MAGIC):
        for b in data:
            if type(b) is int:  # python 2/3 compat
                state ^= b
            else:
                state ^= ord(b)

        return state

    """ Send a request and read the response """
    def command(self, op=None, data=b"", chk=0, wait_response=True, timeout=DEFAULT_TIMEOUT):
        saved_timeout = self._port.timeout
        new_timeout = min(timeout, MAX_TIMEOUT)
        if new_timeout != saved_timeout:
            self._port.timeout = new_timeout

        try:
            if op is not None:
                self.trace("command op=0x%02x data len=%s wait_response=%d timeout=%.3f data=%s",
                           op, len(data), 1 if wait_response else 0, timeout, HexFormatter(data))
                pkt = struct.pack(b'<BBHI', 0x00, op, len(data), chk) + data
                self.write(pkt)

            if not wait_response:
                return

            # tries to get a response until that response has the
            # same operation as the request or a retries limit has
            # exceeded. This is needed for some esp8266s that
            # reply with more sync responses than expected.
            for retry in range(100):
                p = self.read()
                if len(p) < 8:
                    continue
                (resp, op_ret, len_ret, val) = struct.unpack('<BBHI', p[:8])
                if resp != 1:
                    continue
                data = p[8:]

                if op is None or op_ret == op:
                    return val, data
                if byte(data, 0) != 0 and byte(data, 1) == self.ROM_INVALID_RECV_MSG:
                    self.flush_input()  # Unsupported read_reg can result in more than one error response for some reason
                    raise UnsupportedCommandError(self, op)

        finally:
            if new_timeout != saved_timeout:
                self._port.timeout = saved_timeout

        raise FatalError("Response doesn't match request")

    def check_command(self, op_description, op=None, data=b'', chk=0, timeout=DEFAULT_TIMEOUT):
        """
        Execute a command with 'command', check the result code and throw an appropriate
        FatalError if it fails.

        Returns the "result" of a successful command.
        """
        val, data = self.command(op, data, chk, timeout=timeout)

        # things are a bit weird here, bear with us

        # the status bytes are the last 2/4 bytes in the data (depending on chip)
        if len(data) < self.STATUS_BYTES_LENGTH:
            raise FatalError("Failed to %s. Only got %d byte status response." % (op_description, len(data)))
        status_bytes = data[-self.STATUS_BYTES_LENGTH:]
        # we only care if the first one is non-zero. If it is, the second byte is a reason.
        if byte(status_bytes, 0) != 0:
            raise FatalError.WithResult('Failed to %s' % op_description, status_bytes)

        # if we had more data than just the status bytes, return it as the result
        # (this is used by the md5sum command, maybe other commands?)
        if len(data) > self.STATUS_BYTES_LENGTH:
            return data[:-self.STATUS_BYTES_LENGTH]
        else:  # otherwise, just return the 'val' field which comes from the reply header (this is used by read_reg)
            return val

    def flush_input(self):
        self._port.flushInput()
        self._slip_reader = slip_reader(self._port, self.trace)

    def sync(self):
        val, _ = self.command(self.ESP_SYNC, b'\x07\x07\x12\x20' + 32 * b'\x55',
                              timeout=SYNC_TIMEOUT)

        # ROM bootloaders send some non-zero "val" response. The flasher stub sends 0. If we receive 0 then it
        # probably indicates that the chip wasn't or couldn't be reseted properly and esptool is talking to the
        # flasher stub.
        self.sync_stub_detected = val == 0

        for _ in range(7):
            val, _ = self.command()
            self.sync_stub_detected &= val == 0

    def _setDTR(self, state):
        self._port.setDTR(state)

    def _setRTS(self, state):
        self._port.setRTS(state)
        # Work-around for adapters on Windows using the usbser.sys driver:
        # generate a dummy change to DTR so that the set-control-line-state
        # request is sent with the updated RTS state and the same DTR state
        self._port.setDTR(self._port.dtr)

    def _get_pid(self):
        if list_ports is None:
            print("\nListing all serial ports is currently not available. Can't get device PID.")
            return
        active_port = self._port.port

        # Pyserial only identifies regular ports, URL handlers are not supported
        if not active_port.startswith(("COM", "/dev/")):
            print("\nDevice PID identification is only supported on COM and /dev/ serial ports.")
            return
        # Return the real path if the active port is a symlink
        if active_port.startswith("/dev/") and os.path.islink(active_port):
            active_port = os.path.realpath(active_port)

        # The "cu" (call-up) device has to be used for outgoing communication on MacOS
        if sys.platform == "darwin" and "tty" in active_port:
            active_port = [active_port, active_port.replace("tty", "cu")]
        ports = list_ports.comports()
        for p in ports:
            if p.device in active_port:
                return p.pid
        print("\nFailed to get PID of a device on {}, using standard reset sequence.".format(active_port))

    def bootloader_reset(self, usb_jtag_serial=False, extra_delay=False):
        """ Issue a reset-to-bootloader, with USB-JTAG-Serial custom reset sequence option
        """
        # RTS = either CH_PD/EN or nRESET (both active low = chip in reset)
        # DTR = GPIO0 (active low = boot to flasher)
        #
        # DTR & RTS are active low signals,
        # ie True = pin @ 0V, False = pin @ VCC.
        if usb_jtag_serial:
            # Custom reset sequence, which is required when the device
            # is connecting via its USB-JTAG-Serial peripheral
            self._setRTS(False)
            self._setDTR(False)  # Idle
            time.sleep(0.1)
            self._setDTR(True)  # Set IO0
            self._setRTS(False)
            time.sleep(0.1)
            self._setRTS(True)  # Reset. Note dtr/rts calls inverted so we go through (1,1) instead of (0,0)
            self._setDTR(False)
            self._setRTS(True)  # Extra RTS set for RTS as Windows only propagates DTR on RTS setting
            time.sleep(0.1)
            self._setDTR(False)
            self._setRTS(False)
        else:
            # This fpga delay is for Espressif internal use
            fpga_delay = True if self.FPGA_SLOW_BOOT and os.environ.get("ESPTOOL_ENV_FPGA", "").strip() == "1" else False
            delay = 7 if fpga_delay else 0.5 if extra_delay else 0.05  # 0.5 needed for ESP32 rev0 and rev1

            self._setDTR(False)  # IO0=HIGH
            self._setRTS(True)   # EN=LOW, chip in reset
            time.sleep(0.1)
            self._setDTR(True)   # IO0=LOW
            self._setRTS(False)  # EN=HIGH, chip out of reset
            time.sleep(delay)
            self._setDTR(False)  # IO0=HIGH, done

    def _connect_attempt(self, mode='default_reset', usb_jtag_serial=False, extra_delay=False):
        """ A single connection attempt """
        last_error = None
        boot_log_detected = False
        download_mode = False

        # If we're doing no_sync, we're likely communicating as a pass through
        # with an intermediate device to the ESP32
        if mode == "no_reset_no_sync":
            return last_error

        if mode != 'no_reset':
            self._port.flushInput()  # Empty serial buffer to isolate boot log
            self.bootloader_reset(usb_jtag_serial, extra_delay)

            # Detect the ROM boot log and check actual boot mode (ESP32 and later only)
            waiting = self._port.inWaiting()
            read_bytes = self._port.read(waiting)
            data = re.search(b'boot:(0x[0-9a-fA-F]+)(.*waiting for download)?', read_bytes, re.DOTALL)
            if data is not None:
                boot_log_detected = True
                boot_mode = data.group(1)
                download_mode = data.group(2) is not None

        for _ in range(5):
            try:
                self.flush_input()
                self._port.flushOutput()
                self.sync()
                return None
            except FatalError as e:
                print('.', end='')
                sys.stdout.flush()
                time.sleep(0.05)
                last_error = e

        if boot_log_detected:
            last_error = FatalError("Wrong boot mode detected ({})! The chip needs to be in download mode.".format(boot_mode.decode("utf-8")))
            if download_mode:
                last_error = FatalError("Download mode successfully detected, but getting no sync reply: The serial TX path seems to be down.")
        return last_error

    def get_memory_region(self, name):
        """ Returns a tuple of (start, end) for the memory map entry with the given name, or None if it doesn't exist
        """
        try:
            return [(start, end) for (start, end, n) in self.MEMORY_MAP if n == name][0]
        except IndexError:
            return None

    def connect(self, mode='default_reset', attempts=DEFAULT_CONNECT_ATTEMPTS, detecting=False, warnings=True):
        """ Try connecting repeatedly until successful, or giving up """
        if warnings and mode in ['no_reset', 'no_reset_no_sync']:
            print('WARNING: Pre-connection option "{}" was selected.'.format(mode),
                  'Connection may fail if the chip is not in bootloader or flasher stub mode.')
        print('Connecting...', end='')
        sys.stdout.flush()
        last_error = None

        usb_jtag_serial = (mode == 'usb_reset') or (self._get_pid() == self.USB_JTAG_SERIAL_PID)

        try:
            for _, extra_delay in zip(range(attempts) if attempts > 0 else itertools.count(), itertools.cycle((False, True))):
                last_error = self._connect_attempt(mode=mode, usb_jtag_serial=usb_jtag_serial, extra_delay=extra_delay)
                if last_error is None:
                    break
        finally:
            print('')  # end 'Connecting...' line

        if last_error is not None:
            raise FatalError('Failed to connect to %s: %s'
                             '\nFor troubleshooting steps visit: https://github.com/espressif/esptool#troubleshooting' % (self.CHIP_NAME, last_error))

        if not detecting:
            try:
                # check the date code registers match what we expect to see
                chip_magic_value = self.read_reg(ESPLoader.CHIP_DETECT_MAGIC_REG_ADDR)
                if chip_magic_value not in self.CHIP_DETECT_MAGIC_VALUE:
                    actually = None
                    for cls in [ESP8266ROM, ESP32ROM, ESP32S2ROM, ESP32S3BETA2ROM, ESP32S3ROM, ESP32C3ROM, ESP32H2ROM, ESP8684ROM]:
                        if chip_magic_value in cls.CHIP_DETECT_MAGIC_VALUE:
                            actually = cls
                            break
                    if warnings and actually is None:
                        print(("WARNING: This chip doesn't appear to be a %s (chip magic value 0x%08x). "
                               "Probably it is unsupported by this version of esptool.") % (self.CHIP_NAME, chip_magic_value))
                    else:
                        raise FatalError("This chip is %s not %s. Wrong --chip argument?" % (actually.CHIP_NAME, self.CHIP_NAME))
            except UnsupportedCommandError:
                self.secure_download_mode = True
            self._post_connect()
            self.check_chip_id()

    def _post_connect(self):
        """
        Additional initialization hook, may be overridden by the chip-specific class.
        Gets called after connect, and after auto-detection.
        """
        pass

    def read_reg(self, addr, timeout=DEFAULT_TIMEOUT):
        """ Read memory address in target """
        # we don't call check_command here because read_reg() function is called
        # when detecting chip type, and the way we check for success (STATUS_BYTES_LENGTH) is different
        # for different chip types (!)
        val, data = self.command(self.ESP_READ_REG, struct.pack('<I', addr), timeout=timeout)
        if byte(data, 0) != 0:
            raise FatalError.WithResult("Failed to read register address %08x" % addr, data)
        return val

    """ Write to memory address in target """
    def write_reg(self, addr, value, mask=0xFFFFFFFF, delay_us=0, delay_after_us=0):
        command = struct.pack('<IIII', addr, value, mask, delay_us)
        if delay_after_us > 0:
            # add a dummy write to a date register as an excuse to have a delay
            command += struct.pack('<IIII', self.UART_DATE_REG_ADDR, 0, 0, delay_after_us)

        return self.check_command("write target memory", self.ESP_WRITE_REG, command)

    def update_reg(self, addr, mask, new_val):
        """ Update register at 'addr', replace the bits masked out by 'mask'
        with new_val. new_val is shifted left to match the LSB of 'mask'

        Returns just-written value of register.
        """
        shift = _mask_to_shift(mask)
        val = self.read_reg(addr)
        val &= ~mask
        val |= (new_val << shift) & mask
        self.write_reg(addr, val)

        return val

    """ Start downloading an application image to RAM """
    def mem_begin(self, size, blocks, blocksize, offset):
        if self.IS_STUB:  # check we're not going to overwrite a running stub with this data
            stub = self.STUB_CODE
            load_start = offset
            load_end = offset + size
            for (start, end) in [(stub["data_start"], stub["data_start"] + len(stub["data"])),
                                 (stub["text_start"], stub["text_start"] + len(stub["text"]))]:
                if load_start < end and load_end > start:
                    raise FatalError(("Software loader is resident at 0x%08x-0x%08x. "
                                      "Can't load binary at overlapping address range 0x%08x-0x%08x. "
                                      "Either change binary loading address, or use the --no-stub "
                                      "option to disable the software loader.") % (start, end, load_start, load_end))

        return self.check_command("enter RAM download mode", self.ESP_MEM_BEGIN,
                                  struct.pack('<IIII', size, blocks, blocksize, offset))

    """ Send a block of an image to RAM """
    def mem_block(self, data, seq):
        return self.check_command("write to target RAM", self.ESP_MEM_DATA,
                                  struct.pack('<IIII', len(data), seq, 0, 0) + data,
                                  self.checksum(data))

    """ Leave download mode and run the application """
    def mem_finish(self, entrypoint=0):
        # Sending ESP_MEM_END usually sends a correct response back, however sometimes
        # (with ROM loader) the executed code may reset the UART or change the baud rate
        # before the transmit FIFO is empty. So in these cases we set a short timeout and
        # ignore errors.
        timeout = DEFAULT_TIMEOUT if self.IS_STUB else MEM_END_ROM_TIMEOUT
        data = struct.pack('<II', int(entrypoint == 0), entrypoint)
        try:
            return self.check_command("leave RAM download mode", self.ESP_MEM_END,
                                      data=data, timeout=timeout)
        except FatalError:
            if self.IS_STUB:
                raise
            pass

    """ Start downloading to Flash (performs an erase)

    Returns number of blocks (of size self.FLASH_WRITE_SIZE) to write.
    """
    def flash_begin(self, size, offset, begin_rom_encrypted=False):
        num_blocks = (size + self.FLASH_WRITE_SIZE - 1) // self.FLASH_WRITE_SIZE
        erase_size = self.get_erase_size(offset, size)

        t = time.time()
        if self.IS_STUB:
            timeout = DEFAULT_TIMEOUT
        else:
            timeout = timeout_per_mb(ERASE_REGION_TIMEOUT_PER_MB, size)  # ROM performs the erase up front

        params = struct.pack('<IIII', erase_size, num_blocks, self.FLASH_WRITE_SIZE, offset)
        if isinstance(self, (ESP32S2ROM, ESP32S3BETA2ROM, ESP32S3ROM, ESP32C3ROM, ESP32C6BETAROM, ESP32H2ROM, ESP8684ROM)) and not self.IS_STUB:
            params += struct.pack('<I', 1 if begin_rom_encrypted else 0)
        self.check_command("enter Flash download mode", self.ESP_FLASH_BEGIN,
                           params, timeout=timeout)
        if size != 0 and not self.IS_STUB:
            print("Took %.2fs to erase flash block" % (time.time() - t))
        return num_blocks

    """ Write block to flash """
    def flash_block(self, data, seq, timeout=DEFAULT_TIMEOUT):
        self.check_command("write to target Flash after seq %d" % seq,
                           self.ESP_FLASH_DATA,
                           struct.pack('<IIII', len(data), seq, 0, 0) + data,
                           self.checksum(data),
                           timeout=timeout)

    """ Encrypt before writing to flash """
    def flash_encrypt_block(self, data, seq, timeout=DEFAULT_TIMEOUT):
        if isinstance(self, (ESP32S2ROM, ESP32C3ROM, ESP32S3ROM, ESP32H2ROM, ESP8684ROM)) and not self.IS_STUB:
            # ROM support performs the encrypted writes via the normal write command,
            # triggered by flash_begin(begin_rom_encrypted=True)
            return self.flash_block(data, seq, timeout)

        self.check_command("Write encrypted to target Flash after seq %d" % seq,
                           self.ESP_FLASH_ENCRYPT_DATA,
                           struct.pack('<IIII', len(data), seq, 0, 0) + data,
                           self.checksum(data),
                           timeout=timeout)

    """ Leave flash mode and run/reboot """
    def flash_finish(self, reboot=False):
        pkt = struct.pack('<I', int(not reboot))
        # stub sends a reply to this command
        self.check_command("leave Flash mode", self.ESP_FLASH_END, pkt)

    """ Run application code in flash """
    def run(self, reboot=False):
        # Fake flash begin immediately followed by flash end
        self.flash_begin(0, 0)
        self.flash_finish(reboot)

    """ Read SPI flash manufacturer and device id """
    def flash_id(self):
        SPIFLASH_RDID = 0x9F
        return self.run_spiflash_command(SPIFLASH_RDID, b"", 24)

    def get_security_info(self):
        res = self.check_command('get security info', self.ESP_GET_SECURITY_INFO, b'')
        esp32s2 = True if len(res) == 12 else False
        res = struct.unpack("<IBBBBBBBB" if esp32s2 else "<IBBBBBBBBII", res)
        return {
            "flags": res[0],
            "flash_crypt_cnt": res[1],
            "key_purposes": res[2:9],
            "chip_id": None if esp32s2 else res[9],
            "api_version": None if esp32s2 else res[10],
        }

    @esp32s3_or_newer_function_only
    def get_chip_id(self):
        res = self.check_command('get security info', self.ESP_GET_SECURITY_INFO, b'')
        res = struct.unpack("<IBBBBBBBBI", res[:16])  # 4b flags, 1b flash_crypt_cnt, 7*1b key_purposes, 4b chip_id
        chip_id = res[9]  # 2/4 status bytes invariant
        return chip_id

    @classmethod
    def parse_flash_size_arg(cls, arg):
        try:
            return cls.FLASH_SIZES[arg]
        except KeyError:
            raise FatalError("Flash size '%s' is not supported by this chip type. Supported sizes: %s"
                             % (arg, ", ".join(cls.FLASH_SIZES.keys())))

    def run_stub(self, stub=None):
        if stub is None:
            stub = self.STUB_CODE

        if self.sync_stub_detected:
            print("Stub is already running. No upload is necessary.")
            return self.STUB_CLASS(self)

        # Upload
        print("Uploading stub...")
        for field in ['text', 'data']:
            if field in stub:
                offs = stub[field + "_start"]
                length = len(stub[field])
                blocks = (length + self.ESP_RAM_BLOCK - 1) // self.ESP_RAM_BLOCK
                self.mem_begin(length, blocks, self.ESP_RAM_BLOCK, offs)
                for seq in range(blocks):
                    from_offs = seq * self.ESP_RAM_BLOCK
                    to_offs = from_offs + self.ESP_RAM_BLOCK
                    self.mem_block(stub[field][from_offs:to_offs], seq)
        print("Running stub...")
        self.mem_finish(stub['entry'])

        p = self.read()
        if p != b'OHAI':
            raise FatalError("Failed to start stub. Unexpected response: %s" % p)
        print("Stub running...")
        return self.STUB_CLASS(self)

    @stub_and_esp32_function_only
    def flash_defl_begin(self, size, compsize, offset):
        """ Start downloading compressed data to Flash (performs an erase)

        Returns number of blocks (size self.FLASH_WRITE_SIZE) to write.
        """
        num_blocks = (compsize + self.FLASH_WRITE_SIZE - 1) // self.FLASH_WRITE_SIZE
        erase_blocks = (size + self.FLASH_WRITE_SIZE - 1) // self.FLASH_WRITE_SIZE

        t = time.time()
        if self.IS_STUB:
            write_size = size  # stub expects number of bytes here, manages erasing internally
            timeout = DEFAULT_TIMEOUT
        else:
            write_size = erase_blocks * self.FLASH_WRITE_SIZE  # ROM expects rounded up to erase block size
            timeout = timeout_per_mb(ERASE_REGION_TIMEOUT_PER_MB, write_size)  # ROM performs the erase up front
        print("Compressed %d bytes to %d..." % (size, compsize))
        params = struct.pack('<IIII', write_size, num_blocks, self.FLASH_WRITE_SIZE, offset)
        if isinstance(self, (ESP32S2ROM, ESP32S3BETA2ROM, ESP32S3ROM, ESP32C3ROM, ESP32C6BETAROM, ESP32H2ROM, ESP8684ROM)) and not self.IS_STUB:
            params += struct.pack('<I', 0)  # extra param is to enter encrypted flash mode via ROM (not supported currently)
        self.check_command("enter compressed flash mode", self.ESP_FLASH_DEFL_BEGIN, params, timeout=timeout)
        if size != 0 and not self.IS_STUB:
            # (stub erases as it writes, but ROM loaders erase on begin)
            print("Took %.2fs to erase flash block" % (time.time() - t))
        return num_blocks

    """ Write block to flash, send compressed """
    @stub_and_esp32_function_only
    def flash_defl_block(self, data, seq, timeout=DEFAULT_TIMEOUT):
        self.check_command("write compressed data to flash after seq %d" % seq,
                           self.ESP_FLASH_DEFL_DATA, struct.pack('<IIII', len(data), seq, 0, 0) + data, self.checksum(data), timeout=timeout)

    """ Leave compressed flash mode and run/reboot """
    @stub_and_esp32_function_only
    def flash_defl_finish(self, reboot=False):
        if not reboot and not self.IS_STUB:
            # skip sending flash_finish to ROM loader, as this
            # exits the bootloader. Stub doesn't do this.
            return
        pkt = struct.pack('<I', int(not reboot))
        self.check_command("leave compressed flash mode", self.ESP_FLASH_DEFL_END, pkt)
        self.in_bootloader = False

    @stub_and_esp32_function_only
    def flash_md5sum(self, addr, size):
        # the MD5 command returns additional bytes in the standard
        # command reply slot
        timeout = timeout_per_mb(MD5_TIMEOUT_PER_MB, size)
        res = self.check_command('calculate md5sum', self.ESP_SPI_FLASH_MD5, struct.pack('<IIII', addr, size, 0, 0),
                                 timeout=timeout)

        if len(res) == 32:
            return res.decode("utf-8")  # already hex formatted
        elif len(res) == 16:
            return hexify(res).lower()
        else:
            raise FatalError("MD5Sum command returned unexpected result: %r" % res)

    @stub_and_esp32_function_only
    def change_baud(self, baud):
        print("Changing baud rate to %d" % baud)
        # stub takes the new baud rate and the old one
        second_arg = self._port.baudrate if self.IS_STUB else 0
        self.command(self.ESP_CHANGE_BAUDRATE, struct.pack('<II', baud, second_arg))
        print("Changed.")
        self._set_port_baudrate(baud)
        time.sleep(0.05)  # get rid of crap sent during baud rate change
        self.flush_input()

    @stub_function_only
    def erase_flash(self):
        # depending on flash chip model the erase may take this long (maybe longer!)
        self.check_command("erase flash", self.ESP_ERASE_FLASH,
                           timeout=CHIP_ERASE_TIMEOUT)

    @stub_function_only
    def erase_region(self, offset, size):
        if offset % self.FLASH_SECTOR_SIZE != 0:
            raise FatalError("Offset to erase from must be a multiple of 4096")
        if size % self.FLASH_SECTOR_SIZE != 0:
            raise FatalError("Size of data to erase must be a multiple of 4096")
        timeout = timeout_per_mb(ERASE_REGION_TIMEOUT_PER_MB, size)
        self.check_command("erase region", self.ESP_ERASE_REGION, struct.pack('<II', offset, size), timeout=timeout)

    def read_flash_slow(self, offset, length, progress_fn):
        raise NotImplementedInROMError(self, self.read_flash_slow)

    def read_flash(self, offset, length, progress_fn=None):
        if not self.IS_STUB:
            return self.read_flash_slow(offset, length, progress_fn)  # ROM-only routine

        # issue a standard bootloader command to trigger the read
        self.check_command("read flash", self.ESP_READ_FLASH,
                           struct.pack('<IIII',
                                       offset,
                                       length,
                                       self.FLASH_SECTOR_SIZE,
                                       64))
        # now we expect (length // block_size) SLIP frames with the data
        data = b''
        while len(data) < length:
            p = self.read()
            data += p
            if len(data) < length and len(p) < self.FLASH_SECTOR_SIZE:
                raise FatalError('Corrupt data, expected 0x%x bytes but received 0x%x bytes' % (self.FLASH_SECTOR_SIZE, len(p)))
            self.write(struct.pack('<I', len(data)))
            if progress_fn and (len(data) % 1024 == 0 or len(data) == length):
                progress_fn(len(data), length)
        if progress_fn:
            progress_fn(len(data), length)
        if len(data) > length:
            raise FatalError('Read more than expected')

        digest_frame = self.read()
        if len(digest_frame) != 16:
            raise FatalError('Expected digest, got: %s' % hexify(digest_frame))
        expected_digest = hexify(digest_frame).upper()
        digest = hashlib.md5(data).hexdigest().upper()
        if digest != expected_digest:
            raise FatalError('Digest mismatch: expected %s, got %s' % (expected_digest, digest))
        return data

    def flash_spi_attach(self, hspi_arg):
        """Send SPI attach command to enable the SPI flash pins

        ESP8266 ROM does this when you send flash_begin, ESP32 ROM
        has it as a SPI command.
        """
        # last 3 bytes in ESP_SPI_ATTACH argument are reserved values
        arg = struct.pack('<I', hspi_arg)
        if not self.IS_STUB:
            # ESP32 ROM loader takes additional 'is legacy' arg, which is not
            # currently supported in the stub loader or esptool.py (as it's not usually needed.)
            is_legacy = 0
            arg += struct.pack('BBBB', is_legacy, 0, 0, 0)
        self.check_command("configure SPI flash pins", ESP32ROM.ESP_SPI_ATTACH, arg)

    def flash_set_parameters(self, size):
        """Tell the ESP bootloader the parameters of the chip

        Corresponds to the "flashchip" data structure that the ROM
        has in RAM.

        'size' is in bytes.

        All other flash parameters are currently hardcoded (on ESP8266
        these are mostly ignored by ROM code, on ESP32 I'm not sure.)
        """
        fl_id = 0
        total_size = size
        block_size = 64 * 1024
        sector_size = 4 * 1024
        page_size = 256
        status_mask = 0xffff
        self.check_command("set SPI params", ESP32ROM.ESP_SPI_SET_PARAMS,
                           struct.pack('<IIIIII', fl_id, total_size, block_size, sector_size, page_size, status_mask))

    def run_spiflash_command(self, spiflash_command, data=b"", read_bits=0):
        """Run an arbitrary SPI flash command.

        This function uses the "USR_COMMAND" functionality in the ESP
        SPI hardware, rather than the precanned commands supported by
        hardware. So the value of spiflash_command is an actual command
        byte, sent over the wire.

        After writing command byte, writes 'data' to MOSI and then
        reads back 'read_bits' of reply on MISO. Result is a number.
        """

        # SPI_USR register flags
        SPI_USR_COMMAND = (1 << 31)
        SPI_USR_MISO    = (1 << 28)
        SPI_USR_MOSI    = (1 << 27)

        # SPI registers, base address differs ESP32* vs 8266
        base = self.SPI_REG_BASE
        SPI_CMD_REG       = base + 0x00
        SPI_USR_REG       = base + self.SPI_USR_OFFS
        SPI_USR1_REG      = base + self.SPI_USR1_OFFS
        SPI_USR2_REG      = base + self.SPI_USR2_OFFS
        SPI_W0_REG        = base + self.SPI_W0_OFFS

        # following two registers are ESP32 & 32S2/32C3 only
        if self.SPI_MOSI_DLEN_OFFS is not None:
            # ESP32/32S2/32C3 has a more sophisticated way to set up "user" commands
            def set_data_lengths(mosi_bits, miso_bits):
                SPI_MOSI_DLEN_REG = base + self.SPI_MOSI_DLEN_OFFS
                SPI_MISO_DLEN_REG = base + self.SPI_MISO_DLEN_OFFS
                if mosi_bits > 0:
                    self.write_reg(SPI_MOSI_DLEN_REG, mosi_bits - 1)
                if miso_bits > 0:
                    self.write_reg(SPI_MISO_DLEN_REG, miso_bits - 1)
        else:

            def set_data_lengths(mosi_bits, miso_bits):
                SPI_DATA_LEN_REG = SPI_USR1_REG
                SPI_MOSI_BITLEN_S = 17
                SPI_MISO_BITLEN_S = 8
                mosi_mask = 0 if (mosi_bits == 0) else (mosi_bits - 1)
                miso_mask = 0 if (miso_bits == 0) else (miso_bits - 1)
                self.write_reg(SPI_DATA_LEN_REG,
                               (miso_mask << SPI_MISO_BITLEN_S) | (
                                   mosi_mask << SPI_MOSI_BITLEN_S))

        # SPI peripheral "command" bitmasks for SPI_CMD_REG
        SPI_CMD_USR  = (1 << 18)

        # shift values
        SPI_USR2_COMMAND_LEN_SHIFT = 28

        if read_bits > 32:
            raise FatalError("Reading more than 32 bits back from a SPI flash operation is unsupported")
        if len(data) > 64:
            raise FatalError("Writing more than 64 bytes of data with one SPI command is unsupported")

        data_bits = len(data) * 8
        old_spi_usr = self.read_reg(SPI_USR_REG)
        old_spi_usr2 = self.read_reg(SPI_USR2_REG)
        flags = SPI_USR_COMMAND
        if read_bits > 0:
            flags |= SPI_USR_MISO
        if data_bits > 0:
            flags |= SPI_USR_MOSI
        set_data_lengths(data_bits, read_bits)
        self.write_reg(SPI_USR_REG, flags)
        self.write_reg(SPI_USR2_REG,
                       (7 << SPI_USR2_COMMAND_LEN_SHIFT) | spiflash_command)
        if data_bits == 0:
            self.write_reg(SPI_W0_REG, 0)  # clear data register before we read it
        else:
            data = pad_to(data, 4, b'\00')  # pad to 32-bit multiple
            words = struct.unpack("I" * (len(data) // 4), data)
            next_reg = SPI_W0_REG
            for word in words:
                self.write_reg(next_reg, word)
                next_reg += 4
        self.write_reg(SPI_CMD_REG, SPI_CMD_USR)

        def wait_done():
            for _ in range(10):
                if (self.read_reg(SPI_CMD_REG) & SPI_CMD_USR) == 0:
                    return
            raise FatalError("SPI command did not complete in time")
        wait_done()

        status = self.read_reg(SPI_W0_REG)
        # restore some SPI controller registers
        self.write_reg(SPI_USR_REG, old_spi_usr)
        self.write_reg(SPI_USR2_REG, old_spi_usr2)
        return status

    def read_status(self, num_bytes=2):
        """Read up to 24 bits (num_bytes) of SPI flash status register contents
        via RDSR, RDSR2, RDSR3 commands

        Not all SPI flash supports all three commands. The upper 1 or 2
        bytes may be 0xFF.
        """
        SPIFLASH_RDSR  = 0x05
        SPIFLASH_RDSR2 = 0x35
        SPIFLASH_RDSR3 = 0x15

        status = 0
        shift = 0
        for cmd in [SPIFLASH_RDSR, SPIFLASH_RDSR2, SPIFLASH_RDSR3][0:num_bytes]:
            status += self.run_spiflash_command(cmd, read_bits=8) << shift
            shift += 8
        return status

    def write_status(self, new_status, num_bytes=2, set_non_volatile=False):
        """Write up to 24 bits (num_bytes) of new status register

        num_bytes can be 1, 2 or 3.

        Not all flash supports the additional commands to write the
        second and third byte of the status register. When writing 2
        bytes, esptool also sends a 16-byte WRSR command (as some
        flash types use this instead of WRSR2.)

        If the set_non_volatile flag is set, non-volatile bits will
        be set as well as volatile ones (WREN used instead of WEVSR).

        """
        SPIFLASH_WRSR = 0x01
        SPIFLASH_WRSR2 = 0x31
        SPIFLASH_WRSR3 = 0x11
        SPIFLASH_WEVSR = 0x50
        SPIFLASH_WREN = 0x06
        SPIFLASH_WRDI = 0x04

        enable_cmd = SPIFLASH_WREN if set_non_volatile else SPIFLASH_WEVSR

        # try using a 16-bit WRSR (not supported by all chips)
        # this may be redundant, but shouldn't hurt
        if num_bytes == 2:
            self.run_spiflash_command(enable_cmd)
            self.run_spiflash_command(SPIFLASH_WRSR, struct.pack("<H", new_status))

        # also try using individual commands (also not supported by all chips for num_bytes 2 & 3)
        for cmd in [SPIFLASH_WRSR, SPIFLASH_WRSR2, SPIFLASH_WRSR3][0:num_bytes]:
            self.run_spiflash_command(enable_cmd)
            self.run_spiflash_command(cmd, struct.pack("B", new_status & 0xFF))
            new_status >>= 8

        self.run_spiflash_command(SPIFLASH_WRDI)

    def get_crystal_freq(self):
        # Figure out the crystal frequency from the UART clock divider
        # Returns a normalized value in integer MHz (40 or 26 are the only supported values)
        #
        # The logic here is:
        # - We know that our baud rate and the ESP UART baud rate are roughly the same, or we couldn't communicate
        # - We can read the UART clock divider register to know how the ESP derives this from the APB bus frequency
        # - Multiplying these two together gives us the bus frequency which is either the crystal frequency (ESP32)
        #   or double the crystal frequency (ESP8266). See the self.XTAL_CLK_DIVIDER parameter for this factor.
        uart_div = self.read_reg(self.UART_CLKDIV_REG) & self.UART_CLKDIV_MASK
        est_xtal = (self._port.baudrate * uart_div) / 1e6 / self.XTAL_CLK_DIVIDER
        norm_xtal = 40 if est_xtal > 33 else 26
        if abs(norm_xtal - est_xtal) > 1:
            print("WARNING: Detected crystal freq %.2fMHz is quite different to normalized freq %dMHz. Unsupported crystal in use?" % (est_xtal, norm_xtal))
        return norm_xtal

    def hard_reset(self):
        print('Hard resetting via RTS pin...')
        self._setRTS(True)  # EN->LOW
        time.sleep(0.1)
        self._setRTS(False)

    def soft_reset(self, stay_in_bootloader):
        if not self.IS_STUB:
            if stay_in_bootloader:
                return  # ROM bootloader is already in bootloader!
            else:
                # 'run user code' is as close to a soft reset as we can do
                self.flash_begin(0, 0)
                self.flash_finish(False)
        else:
            if stay_in_bootloader:
                # soft resetting from the stub loader
                # will re-load the ROM bootloader
                self.flash_begin(0, 0)
                self.flash_finish(True)
            elif self.CHIP_NAME != "ESP8266":
                raise FatalError("Soft resetting is currently only supported on ESP8266")
            else:
                # running user code from stub loader requires some hacks
                # in the stub loader
                self.command(self.ESP_RUN_USER_CODE, wait_response=False)

    def check_chip_id(self):
        try:
            chip_id = self.get_chip_id()
            if chip_id != self.IMAGE_CHIP_ID:
                print("WARNING: Chip ID {} ({}) doesn't match expected Chip ID {}. esptool may not work correctly."
                      .format(chip_id, self.UNSUPPORTED_CHIPS.get(chip_id, 'Unknown'), self.IMAGE_CHIP_ID))
                # Try to flash anyways by disabling stub
                self.stub_is_disabled = True
        except NotImplementedInROMError:
            pass


class ESP8266ROM(ESPLoader):
    """ Access class for ESP8266 ROM bootloader
    """
    CHIP_NAME = "ESP8266"
    IS_STUB = False

    CHIP_DETECT_MAGIC_VALUE = [0xfff0c101]

    # OTP ROM addresses
    ESP_OTP_MAC0    = 0x3ff00050
    ESP_OTP_MAC1    = 0x3ff00054
    ESP_OTP_MAC3    = 0x3ff0005c

    SPI_REG_BASE    = 0x60000200
    SPI_USR_OFFS    = 0x1c
    SPI_USR1_OFFS   = 0x20
    SPI_USR2_OFFS   = 0x24
    SPI_MOSI_DLEN_OFFS = None
    SPI_MISO_DLEN_OFFS = None
    SPI_W0_OFFS     = 0x40

    UART_CLKDIV_REG = 0x60000014

    XTAL_CLK_DIVIDER = 2

    FLASH_SIZES = {
        '512KB': 0x00,
        '256KB': 0x10,
        '1MB': 0x20,
        '2MB': 0x30,
        '4MB': 0x40,
        '2MB-c1': 0x50,
        '4MB-c1': 0x60,
        '8MB': 0x80,
        '16MB': 0x90,
    }

    BOOTLOADER_FLASH_OFFSET = 0

    MEMORY_MAP = [[0x3FF00000, 0x3FF00010, "DPORT"],
                  [0x3FFE8000, 0x40000000, "DRAM"],
                  [0x40100000, 0x40108000, "IRAM"],
                  [0x40201010, 0x402E1010, "IROM"]]

    def get_efuses(self):
        # Return the 128 bits of ESP8266 efuse as a single Python integer
        result = self.read_reg(0x3ff0005c) << 96
        result |= self.read_reg(0x3ff00058) << 64
        result |= self.read_reg(0x3ff00054) << 32
        result |= self.read_reg(0x3ff00050)
        return result

    def _get_flash_size(self, efuses):
        # rX_Y = EFUSE_DATA_OUTX[Y]
        r0_4 = (efuses & (1 << 4)) != 0
        r3_25 = (efuses & (1 << 121)) != 0
        r3_26 = (efuses & (1 << 122)) != 0
        r3_27 = (efuses & (1 << 123)) != 0

        if r0_4 and not r3_25:
            if not r3_27 and not r3_26:
                return 1
            elif not r3_27 and r3_26:
                return 2
        if not r0_4 and r3_25:
            if not r3_27 and not r3_26:
                return 2
            elif not r3_27 and r3_26:
                return 4
        return -1

    def get_chip_description(self):
        efuses = self.get_efuses()
        is_8285 = (efuses & ((1 << 4) | 1 << 80)) != 0  # One or the other efuse bit is set for ESP8285
        if is_8285:
            flash_size = self._get_flash_size(efuses)
            max_temp = (efuses & (1 << 5)) != 0  # This efuse bit identifies the max flash temperature
            chip_name = {
                1: "ESP8285H08" if max_temp else "ESP8285N08",
                2: "ESP8285H16" if max_temp else "ESP8285N16"
            }.get(flash_size, "ESP8285")
            return chip_name
        return "ESP8266EX"

    def get_chip_features(self):
        features = ["WiFi"]
        if "ESP8285" in self.get_chip_description():
            features += ["Embedded Flash"]
        return features

    def flash_spi_attach(self, hspi_arg):
        if self.IS_STUB:
            super(ESP8266ROM, self).flash_spi_attach(hspi_arg)
        else:
            # ESP8266 ROM has no flash_spi_attach command in serial protocol,
            # but flash_begin will do it
            self.flash_begin(0, 0)

    def flash_set_parameters(self, size):
        # not implemented in ROM, but OK to silently skip for ROM
        if self.IS_STUB:
            super(ESP8266ROM, self).flash_set_parameters(size)

    def chip_id(self):
        """ Read Chip ID from efuse - the equivalent of the SDK system_get_chip_id() function """
        id0 = self.read_reg(self.ESP_OTP_MAC0)
        id1 = self.read_reg(self.ESP_OTP_MAC1)
        return (id0 >> 24) | ((id1 & MAX_UINT24) << 8)

    def read_mac(self):
        """ Read MAC from OTP ROM """
        mac0 = self.read_reg(self.ESP_OTP_MAC0)
        mac1 = self.read_reg(self.ESP_OTP_MAC1)
        mac3 = self.read_reg(self.ESP_OTP_MAC3)
        if (mac3 != 0):
            oui = ((mac3 >> 16) & 0xff, (mac3 >> 8) & 0xff, mac3 & 0xff)
        elif ((mac1 >> 16) & 0xff) == 0:
            oui = (0x18, 0xfe, 0x34)
        elif ((mac1 >> 16) & 0xff) == 1:
            oui = (0xac, 0xd0, 0x74)
        else:
            raise FatalError("Unknown OUI")
        return oui + ((mac1 >> 8) & 0xff, mac1 & 0xff, (mac0 >> 24) & 0xff)

    def get_erase_size(self, offset, size):
        """ Calculate an erase size given a specific size in bytes.

        Provides a workaround for the bootloader erase bug."""

        sectors_per_block = 16
        sector_size = self.FLASH_SECTOR_SIZE
        num_sectors = (size + sector_size - 1) // sector_size
        start_sector = offset // sector_size

        head_sectors = sectors_per_block - (start_sector % sectors_per_block)
        if num_sectors < head_sectors:
            head_sectors = num_sectors

        if num_sectors < 2 * head_sectors:
            return (num_sectors + 1) // 2 * sector_size
        else:
            return (num_sectors - head_sectors) * sector_size

    def override_vddsdio(self, new_voltage):
        raise NotImplementedInROMError("Overriding VDDSDIO setting only applies to ESP32")


class ESP8266StubLoader(ESP8266ROM):
    """ Access class for ESP8266 stub loader, runs on top of ROM.
    """
    FLASH_WRITE_SIZE = 0x4000  # matches MAX_WRITE_BLOCK in stub_loader.c
    IS_STUB = True

    def __init__(self, rom_loader):
        self.secure_download_mode = rom_loader.secure_download_mode
        self._port = rom_loader._port
        self._trace_enabled = rom_loader._trace_enabled
        self.flush_input()  # resets _slip_reader

    def get_erase_size(self, offset, size):
        return size  # stub doesn't have same size bug as ROM loader


ESP8266ROM.STUB_CLASS = ESP8266StubLoader


class ESP32ROM(ESPLoader):
    """Access class for ESP32 ROM bootloader

    """
    CHIP_NAME = "ESP32"
    IMAGE_CHIP_ID = 0
    IS_STUB = False

    FPGA_SLOW_BOOT = True

    CHIP_DETECT_MAGIC_VALUE = [0x00f01d83]

    IROM_MAP_START = 0x400d0000
    IROM_MAP_END   = 0x40400000

    DROM_MAP_START = 0x3F400000
    DROM_MAP_END   = 0x3F800000

    # ESP32 uses a 4 byte status reply
    STATUS_BYTES_LENGTH = 4

    SPI_REG_BASE   = 0x3ff42000
    SPI_USR_OFFS    = 0x1c
    SPI_USR1_OFFS   = 0x20
    SPI_USR2_OFFS   = 0x24
    SPI_MOSI_DLEN_OFFS = 0x28
    SPI_MISO_DLEN_OFFS = 0x2c
    EFUSE_RD_REG_BASE = 0x3ff5a000

    EFUSE_DIS_DOWNLOAD_MANUAL_ENCRYPT_REG = EFUSE_RD_REG_BASE + 0x18
    EFUSE_DIS_DOWNLOAD_MANUAL_ENCRYPT = (1 << 7)  # EFUSE_RD_DISABLE_DL_ENCRYPT

    DR_REG_SYSCON_BASE = 0x3ff66000

    SPI_W0_OFFS = 0x80

    UART_CLKDIV_REG = 0x3ff40014

    XTAL_CLK_DIVIDER = 1

    FLASH_SIZES = {
        '1MB': 0x00,
        '2MB': 0x10,
        '4MB': 0x20,
        '8MB': 0x30,
        '16MB': 0x40
    }

    BOOTLOADER_FLASH_OFFSET = 0x1000

    OVERRIDE_VDDSDIO_CHOICES = ["1.8V", "1.9V", "OFF"]

    MEMORY_MAP = [[0x00000000, 0x00010000, "PADDING"],
                  [0x3F400000, 0x3F800000, "DROM"],
                  [0x3F800000, 0x3FC00000, "EXTRAM_DATA"],
                  [0x3FF80000, 0x3FF82000, "RTC_DRAM"],
                  [0x3FF90000, 0x40000000, "BYTE_ACCESSIBLE"],
                  [0x3FFAE000, 0x40000000, "DRAM"],
                  [0x3FFE0000, 0x3FFFFFFC, "DIRAM_DRAM"],
                  [0x40000000, 0x40070000, "IROM"],
                  [0x40070000, 0x40078000, "CACHE_PRO"],
                  [0x40078000, 0x40080000, "CACHE_APP"],
                  [0x40080000, 0x400A0000, "IRAM"],
                  [0x400A0000, 0x400BFFFC, "DIRAM_IRAM"],
                  [0x400C0000, 0x400C2000, "RTC_IRAM"],
                  [0x400D0000, 0x40400000, "IROM"],
                  [0x50000000, 0x50002000, "RTC_DATA"]]

    FLASH_ENCRYPTED_WRITE_ALIGN = 32

    """ Try to read the BLOCK1 (encryption key) and check if it is valid """

    def is_flash_encryption_key_valid(self):

        """ Bit 0 of efuse_rd_disable[3:0] is mapped to BLOCK1
        this bit is at position 16 in EFUSE_BLK0_RDATA0_REG """
        word0 = self.read_efuse(0)
        rd_disable = (word0 >> 16) & 0x1

        # reading of BLOCK1 is NOT ALLOWED so we assume valid key is programmed
        if rd_disable:
            return True
        else:
            # reading of BLOCK1 is ALLOWED so we will read and verify for non-zero.
            # When ESP32 has not generated AES/encryption key in BLOCK1, the contents will be readable and 0.
            # If the flash encryption is enabled it is expected to have a valid non-zero key. We break out on
            # first occurance of non-zero value
            key_word = [0] * 7
            for i in range(len(key_word)):
                key_word[i] = self.read_efuse(14 + i)
                # key is non-zero so break & return
                if key_word[i] != 0:
                    return True
            return False

    def get_flash_crypt_config(self):
        """ For flash encryption related commands we need to make sure
        user has programmed all the relevant efuse correctly so before
        writing encrypted write_flash_encrypt esptool will verify the values
        of flash_crypt_config to be non zero if they are not read
        protected. If the values are zero a warning will be printed

        bit 3 in efuse_rd_disable[3:0] is mapped to flash_crypt_config
        this bit is at position 19 in EFUSE_BLK0_RDATA0_REG """
        word0 = self.read_efuse(0)
        rd_disable = (word0 >> 19) & 0x1

        if rd_disable == 0:
            """ we can read the flash_crypt_config efuse value
            so go & read it (EFUSE_BLK0_RDATA5_REG[31:28]) """
            word5 = self.read_efuse(5)
            word5 = (word5 >> 28) & 0xF
            return word5
        else:
            # if read of the efuse is disabled we assume it is set correctly
            return 0xF

    def get_encrypted_download_disabled(self):
        if self.read_reg(self.EFUSE_DIS_DOWNLOAD_MANUAL_ENCRYPT_REG) & self.EFUSE_DIS_DOWNLOAD_MANUAL_ENCRYPT:
            return True
        else:
            return False

    def get_pkg_version(self):
        word3 = self.read_efuse(3)
        pkg_version = (word3 >> 9) & 0x07
        pkg_version += ((word3 >> 2) & 0x1) << 3
        return pkg_version

    def get_chip_revision(self):
        word3 = self.read_efuse(3)
        word5 = self.read_efuse(5)
        apb_ctl_date = self.read_reg(self.DR_REG_SYSCON_BASE + 0x7C)

        rev_bit0 = (word3 >> 15) & 0x1
        rev_bit1 = (word5 >> 20) & 0x1
        rev_bit2 = (apb_ctl_date >> 31) & 0x1
        if rev_bit0:
            if rev_bit1:
                if rev_bit2:
                    return 3
                else:
                    return 2
            else:
                return 1
        return 0

    def get_chip_description(self):
        pkg_version = self.get_pkg_version()
        chip_revision = self.get_chip_revision()
        rev3 = (chip_revision == 3)
        single_core = self.read_efuse(3) & (1 << 0)  # CHIP_VER DIS_APP_CPU

        chip_name = {
            0: "ESP32-S0WDQ6" if single_core else "ESP32-D0WDQ6",
            1: "ESP32-S0WD" if single_core else "ESP32-D0WD",
            2: "ESP32-D2WD",
            4: "ESP32-U4WDH",
            5: "ESP32-PICO-V3" if rev3 else "ESP32-PICO-D4",
            6: "ESP32-PICO-V3-02",
        }.get(pkg_version, "unknown ESP32")

        # ESP32-D0WD-V3, ESP32-D0WDQ6-V3
        if chip_name.startswith("ESP32-D0WD") and rev3:
            chip_name += "-V3"

        return "%s (revision %d)" % (chip_name, chip_revision)

    def get_chip_features(self):
        features = ["WiFi"]
        word3 = self.read_efuse(3)

        # names of variables in this section are lowercase
        #  versions of EFUSE names as documented in TRM and
        # ESP-IDF efuse_reg.h

        chip_ver_dis_bt = word3 & (1 << 1)
        if chip_ver_dis_bt == 0:
            features += ["BT"]

        chip_ver_dis_app_cpu = word3 & (1 << 0)
        if chip_ver_dis_app_cpu:
            features += ["Single Core"]
        else:
            features += ["Dual Core"]

        chip_cpu_freq_rated = word3 & (1 << 13)
        if chip_cpu_freq_rated:
            chip_cpu_freq_low = word3 & (1 << 12)
            if chip_cpu_freq_low:
                features += ["160MHz"]
            else:
                features += ["240MHz"]

        pkg_version = self.get_pkg_version()
        if pkg_version in [2, 4, 5, 6]:
            features += ["Embedded Flash"]

        if pkg_version == 6:
            features += ["Embedded PSRAM"]

        word4 = self.read_efuse(4)
        adc_vref = (word4 >> 8) & 0x1F
        if adc_vref:
            features += ["VRef calibration in efuse"]

        blk3_part_res = word3 >> 14 & 0x1
        if blk3_part_res:
            features += ["BLK3 partially reserved"]

        word6 = self.read_efuse(6)
        coding_scheme = word6 & 0x3
        features += ["Coding Scheme %s" % {
            0: "None",
            1: "3/4",
            2: "Repeat (UNSUPPORTED)",
            3: "Invalid"}[coding_scheme]]

        return features

    def read_efuse(self, n):
        """ Read the nth word of the ESP3x EFUSE region. """
        return self.read_reg(self.EFUSE_RD_REG_BASE + (4 * n))

    def chip_id(self):
        raise NotSupportedError(self, "chip_id")

    def read_mac(self):
        """ Read MAC from EFUSE region """
        words = [self.read_efuse(2), self.read_efuse(1)]
        bitstring = struct.pack(">II", *words)
        bitstring = bitstring[2:8]  # trim the 2 byte CRC
        try:
            return tuple(ord(b) for b in bitstring)
        except TypeError:  # Python 3, bitstring elements are already bytes
            return tuple(bitstring)

    def get_erase_size(self, offset, size):
        return size

    def override_vddsdio(self, new_voltage):
        new_voltage = new_voltage.upper()
        if new_voltage not in self.OVERRIDE_VDDSDIO_CHOICES:
            raise FatalError("The only accepted VDDSDIO overrides are '1.8V', '1.9V' and 'OFF'")
        RTC_CNTL_SDIO_CONF_REG = 0x3ff48074
        RTC_CNTL_XPD_SDIO_REG = (1 << 31)
        RTC_CNTL_DREFH_SDIO_M = (3 << 29)
        RTC_CNTL_DREFM_SDIO_M = (3 << 27)
        RTC_CNTL_DREFL_SDIO_M = (3 << 25)
        # RTC_CNTL_SDIO_TIEH = (1 << 23)  # not used here, setting TIEH=1 would set 3.3V output, not safe for esptool.py to do
        RTC_CNTL_SDIO_FORCE = (1 << 22)
        RTC_CNTL_SDIO_PD_EN = (1 << 21)

        reg_val = RTC_CNTL_SDIO_FORCE  # override efuse setting
        reg_val |= RTC_CNTL_SDIO_PD_EN
        if new_voltage != "OFF":
            reg_val |= RTC_CNTL_XPD_SDIO_REG  # enable internal LDO
        if new_voltage == "1.9V":
            reg_val |= (RTC_CNTL_DREFH_SDIO_M | RTC_CNTL_DREFM_SDIO_M | RTC_CNTL_DREFL_SDIO_M)  # boost voltage
        self.write_reg(RTC_CNTL_SDIO_CONF_REG, reg_val)
        print("VDDSDIO regulator set to %s" % new_voltage)

    def read_flash_slow(self, offset, length, progress_fn):
        BLOCK_LEN = 64  # ROM read limit per command (this limit is why it's so slow)

        data = b''
        while len(data) < length:
            block_len = min(BLOCK_LEN, length - len(data))
            r = self.check_command("read flash block", self.ESP_READ_FLASH_SLOW,
                                   struct.pack('<II', offset + len(data), block_len))
            if len(r) < block_len:
                raise FatalError("Expected %d byte block, got %d bytes. Serial errors?" % (block_len, len(r)))
            data += r[:block_len]  # command always returns 64 byte buffer, regardless of how many bytes were actually read from flash
            if progress_fn and (len(data) % 1024 == 0 or len(data) == length):
                progress_fn(len(data), length)
        return data


class ESP32S2ROM(ESP32ROM):
    CHIP_NAME = "ESP32-S2"
    IMAGE_CHIP_ID = 2

    FPGA_SLOW_BOOT = False

    IROM_MAP_START = 0x40080000
    IROM_MAP_END   = 0x40b80000
    DROM_MAP_START = 0x3F000000
    DROM_MAP_END   = 0x3F3F0000

    CHIP_DETECT_MAGIC_VALUE = [0x000007c6]

    SPI_REG_BASE = 0x3f402000
    SPI_USR_OFFS    = 0x18
    SPI_USR1_OFFS   = 0x1c
    SPI_USR2_OFFS   = 0x20
    SPI_MOSI_DLEN_OFFS = 0x24
    SPI_MISO_DLEN_OFFS = 0x28
    SPI_W0_OFFS = 0x58

    MAC_EFUSE_REG = 0x3f41A044  # ESP32-S2 has special block for MAC efuses

    UART_CLKDIV_REG = 0x3f400014

    FLASH_ENCRYPTED_WRITE_ALIGN = 16

    # todo: use espefuse APIs to get this info
    EFUSE_BASE = 0x3f41A000
    EFUSE_RD_REG_BASE = EFUSE_BASE + 0x030  # BLOCK0 read base address

    EFUSE_PURPOSE_KEY0_REG = EFUSE_BASE + 0x34
    EFUSE_PURPOSE_KEY0_SHIFT = 24
    EFUSE_PURPOSE_KEY1_REG = EFUSE_BASE + 0x34
    EFUSE_PURPOSE_KEY1_SHIFT = 28
    EFUSE_PURPOSE_KEY2_REG = EFUSE_BASE + 0x38
    EFUSE_PURPOSE_KEY2_SHIFT = 0
    EFUSE_PURPOSE_KEY3_REG = EFUSE_BASE + 0x38
    EFUSE_PURPOSE_KEY3_SHIFT = 4
    EFUSE_PURPOSE_KEY4_REG = EFUSE_BASE + 0x38
    EFUSE_PURPOSE_KEY4_SHIFT = 8
    EFUSE_PURPOSE_KEY5_REG = EFUSE_BASE + 0x38
    EFUSE_PURPOSE_KEY5_SHIFT = 12

    EFUSE_DIS_DOWNLOAD_MANUAL_ENCRYPT_REG = EFUSE_RD_REG_BASE
    EFUSE_DIS_DOWNLOAD_MANUAL_ENCRYPT = 1 << 19

    PURPOSE_VAL_XTS_AES256_KEY_1 = 2
    PURPOSE_VAL_XTS_AES256_KEY_2 = 3
    PURPOSE_VAL_XTS_AES128_KEY = 4

    UARTDEV_BUF_NO = 0x3ffffd14  # Variable in ROM .bss which indicates the port in use
    UARTDEV_BUF_NO_USB = 2  # Value of the above variable indicating that USB is in use

    USB_RAM_BLOCK = 0x800  # Max block size USB CDC is used

    GPIO_STRAP_REG = 0x3f404038
    GPIO_STRAP_SPI_BOOT_MASK = 0x8   # Not download mode
    RTC_CNTL_OPTION1_REG = 0x3f408128
    RTC_CNTL_FORCE_DOWNLOAD_BOOT_MASK = 0x1  # Is download mode forced over USB?

    MEMORY_MAP = [[0x00000000, 0x00010000, "PADDING"],
                  [0x3F000000, 0x3FF80000, "DROM"],
                  [0x3F500000, 0x3FF80000, "EXTRAM_DATA"],
                  [0x3FF9E000, 0x3FFA0000, "RTC_DRAM"],
                  [0x3FF9E000, 0x40000000, "BYTE_ACCESSIBLE"],
                  [0x3FF9E000, 0x40072000, "MEM_INTERNAL"],
                  [0x3FFB0000, 0x40000000, "DRAM"],
                  [0x40000000, 0x4001A100, "IROM_MASK"],
                  [0x40020000, 0x40070000, "IRAM"],
                  [0x40070000, 0x40072000, "RTC_IRAM"],
                  [0x40080000, 0x40800000, "IROM"],
                  [0x50000000, 0x50002000, "RTC_DATA"]]

    def get_pkg_version(self):
        num_word = 4
        block1_addr = self.EFUSE_BASE + 0x044
        word3 = self.read_reg(block1_addr + (4 * num_word))
        pkg_version = (word3 >> 0) & 0x0F
        return pkg_version

    def get_flash_version(self):
        num_word = 3
        block1_addr = self.EFUSE_BASE + 0x044
        word3 = self.read_reg(block1_addr + (4 * num_word))
        pkg_version = (word3 >> 21) & 0x0F
        return pkg_version

    def get_psram_version(self):
        num_word = 3
        block1_addr = self.EFUSE_BASE + 0x044
        word3 = self.read_reg(block1_addr + (4 * num_word))
        pkg_version = (word3 >> 28) & 0x0F
        return pkg_version

    def get_block2_version(self):
        num_word = 4
        block2_addr = self.EFUSE_BASE + 0x05C
        word4 = self.read_reg(block2_addr + (4 * num_word))
        block2_version = (word4 >> 4) & 0x07
        return block2_version

    def get_chip_description(self):
        chip_name = {
            0: "ESP32-S2",
            1: "ESP32-S2FH2",
            2: "ESP32-S2FH4",
            102: "ESP32-S2FNR2",
            100: "ESP32-S2R2",
        }.get(self.get_flash_version() + self.get_psram_version() * 100, "unknown ESP32-S2")

        return "%s" % (chip_name)

    def get_chip_features(self):
        features = ["WiFi"]

        if self.secure_download_mode:
            features += ["Secure Download Mode Enabled"]

        flash_version = {
            0: "No Embedded Flash",
            1: "Embedded Flash 2MB",
            2: "Embedded Flash 4MB",
        }.get(self.get_flash_version(), "Unknown Embedded Flash")
        features += [flash_version]

        psram_version = {
            0: "No Embedded PSRAM",
            1: "Embedded PSRAM 2MB",
            2: "Embedded PSRAM 4MB",
        }.get(self.get_psram_version(), "Unknown Embedded PSRAM")
        features += [psram_version]

        block2_version = {
            0: "No calibration in BLK2 of efuse",
            1: "ADC and temperature sensor calibration in BLK2 of efuse V1",
            2: "ADC and temperature sensor calibration in BLK2 of efuse V2",
        }.get(self.get_block2_version(), "Unknown Calibration in BLK2")
        features += [block2_version]

        return features

    def get_crystal_freq(self):
        # ESP32-S2 XTAL is fixed to 40MHz
        return 40

    def override_vddsdio(self, new_voltage):
        raise NotImplementedInROMError("VDD_SDIO overrides are not supported for ESP32-S2")

    def read_mac(self):
        mac0 = self.read_reg(self.MAC_EFUSE_REG)
        mac1 = self.read_reg(self.MAC_EFUSE_REG + 4)  # only bottom 16 bits are MAC
        bitstring = struct.pack(">II", mac1, mac0)[2:]
        try:
            return tuple(ord(b) for b in bitstring)
        except TypeError:  # Python 3, bitstring elements are already bytes
            return tuple(bitstring)

    def get_flash_crypt_config(self):
        return None  # doesn't exist on ESP32-S2

    def get_key_block_purpose(self, key_block):
        if key_block < 0 or key_block > 5:
            raise FatalError("Valid key block numbers must be in range 0-5")

        reg, shift = [(self.EFUSE_PURPOSE_KEY0_REG, self.EFUSE_PURPOSE_KEY0_SHIFT),
                      (self.EFUSE_PURPOSE_KEY1_REG, self.EFUSE_PURPOSE_KEY1_SHIFT),
                      (self.EFUSE_PURPOSE_KEY2_REG, self.EFUSE_PURPOSE_KEY2_SHIFT),
                      (self.EFUSE_PURPOSE_KEY3_REG, self.EFUSE_PURPOSE_KEY3_SHIFT),
                      (self.EFUSE_PURPOSE_KEY4_REG, self.EFUSE_PURPOSE_KEY4_SHIFT),
                      (self.EFUSE_PURPOSE_KEY5_REG, self.EFUSE_PURPOSE_KEY5_SHIFT)][key_block]
        return (self.read_reg(reg) >> shift) & 0xF

    def is_flash_encryption_key_valid(self):
        # Need to see either an AES-128 key or two AES-256 keys
        purposes = [self.get_key_block_purpose(b) for b in range(6)]

        if any(p == self.PURPOSE_VAL_XTS_AES128_KEY for p in purposes):
            return True

        return any(p == self.PURPOSE_VAL_XTS_AES256_KEY_1 for p in purposes) \
            and any(p == self.PURPOSE_VAL_XTS_AES256_KEY_2 for p in purposes)

    def uses_usb(self, _cache=[]):
        if self.secure_download_mode:
            return False  # can't detect native USB in secure download mode
        if not _cache:
            buf_no = self.read_reg(self.UARTDEV_BUF_NO) & 0xff
            _cache.append(buf_no == self.UARTDEV_BUF_NO_USB)
        return _cache[0]

    def _post_connect(self):
        if self.uses_usb():
            self.ESP_RAM_BLOCK = self.USB_RAM_BLOCK

    def _check_if_can_reset(self):
        """
        Check the strapping register to see if we can reset out of download mode.
        """
        if os.getenv("ESPTOOL_TESTING") is not None:
            print("ESPTOOL_TESTING is set, ignoring strapping mode check")
            # Esptool tests over USB CDC run with GPIO0 strapped low, don't complain in this case.
            return
        strap_reg = self.read_reg(self.GPIO_STRAP_REG)
        force_dl_reg = self.read_reg(self.RTC_CNTL_OPTION1_REG)
        if strap_reg & self.GPIO_STRAP_SPI_BOOT_MASK == 0 and force_dl_reg & self.RTC_CNTL_FORCE_DOWNLOAD_BOOT_MASK == 0:
            print("WARNING: {} chip was placed into download mode using GPIO0.\n"
                  "esptool.py can not exit the download mode over USB. "
                  "To run the app, reset the chip manually.\n"
                  "To suppress this note, set --after option to 'no_reset'.".format(self.get_chip_description()))
            raise SystemExit(1)

    def hard_reset(self):
        if self.uses_usb():
            self._check_if_can_reset()

        print('Hard resetting via RTS pin...')
        self._setRTS(True)  # EN->LOW
        if self.uses_usb():
            # Give the chip some time to come out of reset, to be able to handle further DTR/RTS transitions
            time.sleep(0.2)
            self._setRTS(False)
            time.sleep(0.2)
        else:
            self._setRTS(False)


class ESP32S3ROM(ESP32ROM):
    CHIP_NAME = "ESP32-S3"

    IMAGE_CHIP_ID = 9

    CHIP_DETECT_MAGIC_VALUE = [0x9]

    FPGA_SLOW_BOOT = False

    IROM_MAP_START = 0x42000000
    IROM_MAP_END   = 0x44000000
    DROM_MAP_START = 0x3c000000
    DROM_MAP_END   = 0x3e000000

    UART_DATE_REG_ADDR = 0x60000080

    SPI_REG_BASE = 0x60002000
    SPI_USR_OFFS    = 0x18
    SPI_USR1_OFFS   = 0x1c
    SPI_USR2_OFFS   = 0x20
    SPI_MOSI_DLEN_OFFS = 0x24
    SPI_MISO_DLEN_OFFS = 0x28
    SPI_W0_OFFS = 0x58

    FLASH_ENCRYPTED_WRITE_ALIGN = 16

    # todo: use espefuse APIs to get this info
    EFUSE_BASE = 0x60007000  # BLOCK0 read base address
    MAC_EFUSE_REG = EFUSE_BASE + 0x044

    EFUSE_RD_REG_BASE = EFUSE_BASE + 0x030  # BLOCK0 read base address

    EFUSE_PURPOSE_KEY0_REG = EFUSE_BASE + 0x34
    EFUSE_PURPOSE_KEY0_SHIFT = 24
    EFUSE_PURPOSE_KEY1_REG = EFUSE_BASE + 0x34
    EFUSE_PURPOSE_KEY1_SHIFT = 28
    EFUSE_PURPOSE_KEY2_REG = EFUSE_BASE + 0x38
    EFUSE_PURPOSE_KEY2_SHIFT = 0
    EFUSE_PURPOSE_KEY3_REG = EFUSE_BASE + 0x38
    EFUSE_PURPOSE_KEY3_SHIFT = 4
    EFUSE_PURPOSE_KEY4_REG = EFUSE_BASE + 0x38
    EFUSE_PURPOSE_KEY4_SHIFT = 8
    EFUSE_PURPOSE_KEY5_REG = EFUSE_BASE + 0x38
    EFUSE_PURPOSE_KEY5_SHIFT = 12

    EFUSE_DIS_DOWNLOAD_MANUAL_ENCRYPT_REG = EFUSE_RD_REG_BASE
    EFUSE_DIS_DOWNLOAD_MANUAL_ENCRYPT = 1 << 20

    PURPOSE_VAL_XTS_AES256_KEY_1 = 2
    PURPOSE_VAL_XTS_AES256_KEY_2 = 3
    PURPOSE_VAL_XTS_AES128_KEY = 4

    UARTDEV_BUF_NO = 0x3fcef14c  # Variable in ROM .bss which indicates the port in use
    UARTDEV_BUF_NO_USB = 3  # Value of the above variable indicating that USB is in use

    USB_RAM_BLOCK = 0x800  # Max block size USB CDC is used

    GPIO_STRAP_REG = 0x60004038
    GPIO_STRAP_SPI_BOOT_MASK = 0x8   # Not download mode
    RTC_CNTL_OPTION1_REG = 0x6000812C
    RTC_CNTL_FORCE_DOWNLOAD_BOOT_MASK = 0x1  # Is download mode forced over USB?

    UART_CLKDIV_REG = 0x60000014

    MEMORY_MAP = [[0x00000000, 0x00010000, "PADDING"],
                  [0x3C000000, 0x3D000000, "DROM"],
                  [0x3D000000, 0x3E000000, "EXTRAM_DATA"],
                  [0x600FE000, 0x60100000, "RTC_DRAM"],
                  [0x3FC88000, 0x3FD00000, "BYTE_ACCESSIBLE"],
                  [0x3FC88000, 0x403E2000, "MEM_INTERNAL"],
                  [0x3FC88000, 0x3FD00000, "DRAM"],
                  [0x40000000, 0x4001A100, "IROM_MASK"],
                  [0x40370000, 0x403E0000, "IRAM"],
                  [0x600FE000, 0x60100000, "RTC_IRAM"],
                  [0x42000000, 0x42800000, "IROM"],
                  [0x50000000, 0x50002000, "RTC_DATA"]]

    def get_chip_description(self):
        return "ESP32-S3"

    def get_chip_features(self):
        return ["WiFi", "BLE"]

    def get_crystal_freq(self):
        # ESP32S3 XTAL is fixed to 40MHz
        return 40

    def get_flash_crypt_config(self):
        return None  # doesn't exist on ESP32-S3

    def get_key_block_purpose(self, key_block):
        if key_block < 0 or key_block > 5:
            raise FatalError("Valid key block numbers must be in range 0-5")

        reg, shift = [(self.EFUSE_PURPOSE_KEY0_REG, self.EFUSE_PURPOSE_KEY0_SHIFT),
                      (self.EFUSE_PURPOSE_KEY1_REG, self.EFUSE_PURPOSE_KEY1_SHIFT),
                      (self.EFUSE_PURPOSE_KEY2_REG, self.EFUSE_PURPOSE_KEY2_SHIFT),
                      (self.EFUSE_PURPOSE_KEY3_REG, self.EFUSE_PURPOSE_KEY3_SHIFT),
                      (self.EFUSE_PURPOSE_KEY4_REG, self.EFUSE_PURPOSE_KEY4_SHIFT),
                      (self.EFUSE_PURPOSE_KEY5_REG, self.EFUSE_PURPOSE_KEY5_SHIFT)][key_block]
        return (self.read_reg(reg) >> shift) & 0xF

    def is_flash_encryption_key_valid(self):
        # Need to see either an AES-128 key or two AES-256 keys
        purposes = [self.get_key_block_purpose(b) for b in range(6)]

        if any(p == self.PURPOSE_VAL_XTS_AES128_KEY for p in purposes):
            return True

        return any(p == self.PURPOSE_VAL_XTS_AES256_KEY_1 for p in purposes) \
            and any(p == self.PURPOSE_VAL_XTS_AES256_KEY_2 for p in purposes)

    def override_vddsdio(self, new_voltage):
        raise NotImplementedInROMError("VDD_SDIO overrides are not supported for ESP32-S3")

    def read_mac(self):
        mac0 = self.read_reg(self.MAC_EFUSE_REG)
        mac1 = self.read_reg(self.MAC_EFUSE_REG + 4)  # only bottom 16 bits are MAC
        bitstring = struct.pack(">II", mac1, mac0)[2:]
        try:
            return tuple(ord(b) for b in bitstring)
        except TypeError:  # Python 3, bitstring elements are already bytes
            return tuple(bitstring)

    def uses_usb(self, _cache=[]):
        if self.secure_download_mode:
            return False  # can't detect native USB in secure download mode
        if not _cache:
            buf_no = self.read_reg(self.UARTDEV_BUF_NO) & 0xff
            _cache.append(buf_no == self.UARTDEV_BUF_NO_USB)
        return _cache[0]

    def _post_connect(self):
        if self.uses_usb():
            self.ESP_RAM_BLOCK = self.USB_RAM_BLOCK

    def _check_if_can_reset(self):
        """
        Check the strapping register to see if we can reset out of download mode.
        """
        if os.getenv("ESPTOOL_TESTING") is not None:
            print("ESPTOOL_TESTING is set, ignoring strapping mode check")
            # Esptool tests over USB CDC run with GPIO0 strapped low, don't complain in this case.
            return
        strap_reg = self.read_reg(self.GPIO_STRAP_REG)
        force_dl_reg = self.read_reg(self.RTC_CNTL_OPTION1_REG)
        if strap_reg & self.GPIO_STRAP_SPI_BOOT_MASK == 0 and force_dl_reg & self.RTC_CNTL_FORCE_DOWNLOAD_BOOT_MASK == 0:
            print("WARNING: {} chip was placed into download mode using GPIO0.\n"
                  "esptool.py can not exit the download mode over USB. "
                  "To run the app, reset the chip manually.\n"
                  "To suppress this note, set --after option to 'no_reset'.".format(self.get_chip_description()))
            raise SystemExit(1)

    def hard_reset(self):
        if self.uses_usb():
            self._check_if_can_reset()

        print('Hard resetting via RTS pin...')
        self._setRTS(True)  # EN->LOW
        if self.uses_usb():
            # Give the chip some time to come out of reset, to be able to handle further DTR/RTS transitions
            time.sleep(0.2)
            self._setRTS(False)
            time.sleep(0.2)
        else:
            self._setRTS(False)


class ESP32S3BETA2ROM(ESP32S3ROM):
    CHIP_NAME = "ESP32-S3(beta2)"
    IMAGE_CHIP_ID = 4

    CHIP_DETECT_MAGIC_VALUE = [0xeb004136]

    EFUSE_BASE = 0x6001A000  # BLOCK0 read base address

    def get_chip_description(self):
        return "ESP32-S3(beta2)"


class ESP32C3ROM(ESP32ROM):
    CHIP_NAME = "ESP32-C3"
    IMAGE_CHIP_ID = 5

    FPGA_SLOW_BOOT = False

    IROM_MAP_START = 0x42000000
    IROM_MAP_END   = 0x42800000
    DROM_MAP_START = 0x3c000000
    DROM_MAP_END   = 0x3c800000

    SPI_REG_BASE = 0x60002000
    SPI_USR_OFFS    = 0x18
    SPI_USR1_OFFS   = 0x1C
    SPI_USR2_OFFS   = 0x20
    SPI_MOSI_DLEN_OFFS = 0x24
    SPI_MISO_DLEN_OFFS = 0x28
    SPI_W0_OFFS = 0x58

    BOOTLOADER_FLASH_OFFSET = 0x0

    # Magic value for ESP32C3 eco 1+2 and ESP32C3 eco3 respectivly
    CHIP_DETECT_MAGIC_VALUE = [0x6921506f, 0x1b31506f]

    UART_DATE_REG_ADDR = 0x60000000 + 0x7c

    EFUSE_BASE = 0x60008800
    MAC_EFUSE_REG  = EFUSE_BASE + 0x044

    EFUSE_RD_REG_BASE = EFUSE_BASE + 0x030  # BLOCK0 read base address

    EFUSE_PURPOSE_KEY0_REG = EFUSE_BASE + 0x34
    EFUSE_PURPOSE_KEY0_SHIFT = 24
    EFUSE_PURPOSE_KEY1_REG = EFUSE_BASE + 0x34
    EFUSE_PURPOSE_KEY1_SHIFT = 28
    EFUSE_PURPOSE_KEY2_REG = EFUSE_BASE + 0x38
    EFUSE_PURPOSE_KEY2_SHIFT = 0
    EFUSE_PURPOSE_KEY3_REG = EFUSE_BASE + 0x38
    EFUSE_PURPOSE_KEY3_SHIFT = 4
    EFUSE_PURPOSE_KEY4_REG = EFUSE_BASE + 0x38
    EFUSE_PURPOSE_KEY4_SHIFT = 8
    EFUSE_PURPOSE_KEY5_REG = EFUSE_BASE + 0x38
    EFUSE_PURPOSE_KEY5_SHIFT = 12

    EFUSE_DIS_DOWNLOAD_MANUAL_ENCRYPT_REG = EFUSE_RD_REG_BASE
    EFUSE_DIS_DOWNLOAD_MANUAL_ENCRYPT = 1 << 20

    PURPOSE_VAL_XTS_AES128_KEY = 4

    GPIO_STRAP_REG = 0x3f404038

    FLASH_ENCRYPTED_WRITE_ALIGN = 16

    MEMORY_MAP = [[0x00000000, 0x00010000, "PADDING"],
                  [0x3C000000, 0x3C800000, "DROM"],
                  [0x3FC80000, 0x3FCE0000, "DRAM"],
                  [0x3FC88000, 0x3FD00000, "BYTE_ACCESSIBLE"],
                  [0x3FF00000, 0x3FF20000, "DROM_MASK"],
                  [0x40000000, 0x40060000, "IROM_MASK"],
                  [0x42000000, 0x42800000, "IROM"],
                  [0x4037C000, 0x403E0000, "IRAM"],
                  [0x50000000, 0x50002000, "RTC_IRAM"],
                  [0x50000000, 0x50002000, "RTC_DRAM"],
                  [0x600FE000, 0x60100000, "MEM_INTERNAL2"]]

    def get_pkg_version(self):
        num_word = 3
        block1_addr = self.EFUSE_BASE + 0x044
        word3 = self.read_reg(block1_addr + (4 * num_word))
        pkg_version = (word3 >> 21) & 0x07
        return pkg_version

    def get_chip_revision(self):
        # reads WAFER_VERSION field from EFUSE_RD_MAC_SPI_SYS_3_REG
        block1_addr = self.EFUSE_BASE + 0x044
        num_word = 3
        pos = 18
        return (self.read_reg(block1_addr + (4 * num_word)) & (0x7 << pos)) >> pos

    def get_chip_description(self):
        chip_name = {
            0: "ESP32-C3",
        }.get(self.get_pkg_version(), "unknown ESP32-C3")
        chip_revision = self.get_chip_revision()

        return "%s (revision %d)" % (chip_name, chip_revision)

    def get_chip_features(self):
        return ["Wi-Fi"]

    def get_crystal_freq(self):
        # ESP32C3 XTAL is fixed to 40MHz
        return 40

    def override_vddsdio(self, new_voltage):
        raise NotImplementedInROMError("VDD_SDIO overrides are not supported for ESP32-C3")

    def read_mac(self):
        mac0 = self.read_reg(self.MAC_EFUSE_REG)
        mac1 = self.read_reg(self.MAC_EFUSE_REG + 4)  # only bottom 16 bits are MAC
        bitstring = struct.pack(">II", mac1, mac0)[2:]
        try:
            return tuple(ord(b) for b in bitstring)
        except TypeError:  # Python 3, bitstring elements are already bytes
            return tuple(bitstring)

    def get_flash_crypt_config(self):
        return None  # doesn't exist on ESP32-C3

    def get_key_block_purpose(self, key_block):
        if key_block < 0 or key_block > 5:
            raise FatalError("Valid key block numbers must be in range 0-5")

        reg, shift = [(self.EFUSE_PURPOSE_KEY0_REG, self.EFUSE_PURPOSE_KEY0_SHIFT),
                      (self.EFUSE_PURPOSE_KEY1_REG, self.EFUSE_PURPOSE_KEY1_SHIFT),
                      (self.EFUSE_PURPOSE_KEY2_REG, self.EFUSE_PURPOSE_KEY2_SHIFT),
                      (self.EFUSE_PURPOSE_KEY3_REG, self.EFUSE_PURPOSE_KEY3_SHIFT),
                      (self.EFUSE_PURPOSE_KEY4_REG, self.EFUSE_PURPOSE_KEY4_SHIFT),
                      (self.EFUSE_PURPOSE_KEY5_REG, self.EFUSE_PURPOSE_KEY5_SHIFT)][key_block]
        return (self.read_reg(reg) >> shift) & 0xF

    def is_flash_encryption_key_valid(self):
        # Need to see an AES-128 key
        purposes = [self.get_key_block_purpose(b) for b in range(6)]

        return any(p == self.PURPOSE_VAL_XTS_AES128_KEY for p in purposes)


class ESP32H2ROM(ESP32ROM):
    CHIP_NAME = "ESP32-H2"
    IMAGE_CHIP_ID = 10

    IROM_MAP_START = 0x42000000
    IROM_MAP_END   = 0x42800000
    DROM_MAP_START = 0x3c000000
    DROM_MAP_END   = 0x3c800000

    SPI_REG_BASE = 0x60002000
    SPI_USR_OFFS    = 0x18
    SPI_USR1_OFFS   = 0x1C
    SPI_USR2_OFFS   = 0x20
    SPI_MOSI_DLEN_OFFS = 0x24
    SPI_MISO_DLEN_OFFS = 0x28
    SPI_W0_OFFS = 0x58

    BOOTLOADER_FLASH_OFFSET = 0x0

    CHIP_DETECT_MAGIC_VALUE = [0xca26cc22]

    UART_DATE_REG_ADDR = 0x60000000 + 0x7c

    EFUSE_BASE = 0x6001A000
    MAC_EFUSE_REG  = EFUSE_BASE + 0x044

    EFUSE_RD_REG_BASE = EFUSE_BASE + 0x030  # BLOCK0 read base address

    EFUSE_PURPOSE_KEY0_REG = EFUSE_BASE + 0x34
    EFUSE_PURPOSE_KEY0_SHIFT = 24
    EFUSE_PURPOSE_KEY1_REG = EFUSE_BASE + 0x34
    EFUSE_PURPOSE_KEY1_SHIFT = 28
    EFUSE_PURPOSE_KEY2_REG = EFUSE_BASE + 0x38
    EFUSE_PURPOSE_KEY2_SHIFT = 0
    EFUSE_PURPOSE_KEY3_REG = EFUSE_BASE + 0x38
    EFUSE_PURPOSE_KEY3_SHIFT = 4
    EFUSE_PURPOSE_KEY4_REG = EFUSE_BASE + 0x38
    EFUSE_PURPOSE_KEY4_SHIFT = 8
    EFUSE_PURPOSE_KEY5_REG = EFUSE_BASE + 0x38
    EFUSE_PURPOSE_KEY5_SHIFT = 12

    EFUSE_DIS_DOWNLOAD_MANUAL_ENCRYPT_REG = EFUSE_RD_REG_BASE
    EFUSE_DIS_DOWNLOAD_MANUAL_ENCRYPT = 1 << 20

    PURPOSE_VAL_XTS_AES128_KEY = 4

    GPIO_STRAP_REG = 0x3f404038

    FLASH_ENCRYPTED_WRITE_ALIGN = 16

    MEMORY_MAP = []

    def get_pkg_version(self):
        num_word = 3
        block1_addr = self.EFUSE_BASE + 0x044
        word3 = self.read_reg(block1_addr + (4 * num_word))
        pkg_version = (word3 >> 21) & 0x0F
        return pkg_version

    def get_chip_revision(self):
        # reads WAFER_VERSION field from EFUSE_RD_MAC_SPI_SYS_3_REG
        block1_addr = self.EFUSE_BASE + 0x044
        num_word = 3
        pos = 18
        return (self.read_reg(block1_addr + (4 * num_word)) & (0x7 << pos)) >> pos

    def get_chip_description(self):
        chip_name = {
            0: "ESP32-H2",
        }.get(self.get_pkg_version(), "unknown ESP32-H2")
        chip_revision = self.get_chip_revision()

        return "%s (revision %d)" % (chip_name, chip_revision)

    def get_chip_features(self):
        return ["BLE/802.15.4"]

    def get_crystal_freq(self):
        return 40

    def override_vddsdio(self, new_voltage):
        raise NotImplementedInROMError("VDD_SDIO overrides are not supported for ESP32-H2")

    def read_mac(self):
        mac0 = self.read_reg(self.MAC_EFUSE_REG)
        mac1 = self.read_reg(self.MAC_EFUSE_REG + 4)  # only bottom 16 bits are MAC
        bitstring = struct.pack(">II", mac1, mac0)[2:]
        try:
            return tuple(ord(b) for b in bitstring)
        except TypeError:  # Python 3, bitstring elements are already bytes
            return tuple(bitstring)

    def get_flash_crypt_config(self):
        return None  # doesn't exist on ESP32-H2

    def get_key_block_purpose(self, key_block):
        if key_block < 0 or key_block > 5:
            raise FatalError("Valid key block numbers must be in range 0-5")

        reg, shift = [(self.EFUSE_PURPOSE_KEY0_REG, self.EFUSE_PURPOSE_KEY0_SHIFT),
                      (self.EFUSE_PURPOSE_KEY1_REG, self.EFUSE_PURPOSE_KEY1_SHIFT),
                      (self.EFUSE_PURPOSE_KEY2_REG, self.EFUSE_PURPOSE_KEY2_SHIFT),
                      (self.EFUSE_PURPOSE_KEY3_REG, self.EFUSE_PURPOSE_KEY3_SHIFT),
                      (self.EFUSE_PURPOSE_KEY4_REG, self.EFUSE_PURPOSE_KEY4_SHIFT),
                      (self.EFUSE_PURPOSE_KEY5_REG, self.EFUSE_PURPOSE_KEY5_SHIFT)][key_block]
        return (self.read_reg(reg) >> shift) & 0xF

    def is_flash_encryption_key_valid(self):
        # Need to see an AES-128 key
        purposes = [self.get_key_block_purpose(b) for b in range(6)]

        return any(p == self.PURPOSE_VAL_XTS_AES128_KEY for p in purposes)


class ESP8684ROM(ESP32C3ROM):
    CHIP_NAME = "ESP8684"
    IMAGE_CHIP_ID = 12

    CHIP_DETECT_MAGIC_VALUE = [0x6451806f]

    def get_pkg_version(self):
        num_word = 3
        block1_addr = self.EFUSE_BASE + 0x044
        word3 = self.read_reg(block1_addr + (4 * num_word))
        pkg_version = (word3 >> 21) & 0x0F
        return pkg_version

    def get_chip_description(self):
        chip_name = {
            0: "ESP8684",
        }.get(self.get_pkg_version(), "unknown ESP8684")
        chip_revision = self.get_chip_revision()

        return "%s (revision %d)" % (chip_name, chip_revision)


class ESP32C6BETAROM(ESP32C3ROM):
    CHIP_NAME = "ESP32-C6(beta)"
    IMAGE_CHIP_ID = 7

    CHIP_DETECT_MAGIC_VALUE = [0x0da1806f]

    UART_DATE_REG_ADDR = 0x00000500

    def get_chip_description(self):
        chip_name = {
            0: "ESP32-C6",
        }.get(self.get_pkg_version(), "unknown ESP32-C6")
        chip_revision = self.get_chip_revision()

        return "%s (revision %d)" % (chip_name, chip_revision)


class ESP32StubLoader(ESP32ROM):
    """ Access class for ESP32 stub loader, runs on top of ROM.
    """
    FLASH_WRITE_SIZE = 0x4000  # matches MAX_WRITE_BLOCK in stub_loader.c
    STATUS_BYTES_LENGTH = 2  # same as ESP8266, different to ESP32 ROM
    IS_STUB = True

    def __init__(self, rom_loader):
        self.secure_download_mode = rom_loader.secure_download_mode
        self._port = rom_loader._port
        self._trace_enabled = rom_loader._trace_enabled
        self.flush_input()  # resets _slip_reader


ESP32ROM.STUB_CLASS = ESP32StubLoader


class ESP32S2StubLoader(ESP32S2ROM):
    """ Access class for ESP32-S2 stub loader, runs on top of ROM.

    (Basically the same as ESP32StubLoader, but different base class.
    Can possibly be made into a mixin.)
    """
    FLASH_WRITE_SIZE = 0x4000  # matches MAX_WRITE_BLOCK in stub_loader.c
    STATUS_BYTES_LENGTH = 2  # same as ESP8266, different to ESP32 ROM
    IS_STUB = True

    def __init__(self, rom_loader):
        self.secure_download_mode = rom_loader.secure_download_mode
        self._port = rom_loader._port
        self._trace_enabled = rom_loader._trace_enabled
        self.flush_input()  # resets _slip_reader

        if rom_loader.uses_usb():
            self.ESP_RAM_BLOCK = self.USB_RAM_BLOCK
            self.FLASH_WRITE_SIZE = self.USB_RAM_BLOCK


ESP32S2ROM.STUB_CLASS = ESP32S2StubLoader


class ESP32S3BETA2StubLoader(ESP32S3BETA2ROM):
    """ Access class for ESP32S3 stub loader, runs on top of ROM.

    (Basically the same as ESP32StubLoader, but different base class.
    Can possibly be made into a mixin.)
    """
    FLASH_WRITE_SIZE = 0x4000  # matches MAX_WRITE_BLOCK in stub_loader.c
    STATUS_BYTES_LENGTH = 2  # same as ESP8266, different to ESP32 ROM
    IS_STUB = True

    def __init__(self, rom_loader):
        self.secure_download_mode = rom_loader.secure_download_mode
        self._port = rom_loader._port
        self._trace_enabled = rom_loader._trace_enabled
        self.flush_input()  # resets _slip_reader


ESP32S3BETA2ROM.STUB_CLASS = ESP32S3BETA2StubLoader


class ESP32S3StubLoader(ESP32S3ROM):
    """ Access class for ESP32S3 stub loader, runs on top of ROM.

    (Basically the same as ESP32StubLoader, but different base class.
    Can possibly be made into a mixin.)
    """
    FLASH_WRITE_SIZE = 0x4000  # matches MAX_WRITE_BLOCK in stub_loader.c
    STATUS_BYTES_LENGTH = 2  # same as ESP8266, different to ESP32 ROM
    IS_STUB = True

    def __init__(self, rom_loader):
        self.secure_download_mode = rom_loader.secure_download_mode
        self._port = rom_loader._port
        self._trace_enabled = rom_loader._trace_enabled
        self.flush_input()  # resets _slip_reader

        if rom_loader.uses_usb():
            self.ESP_RAM_BLOCK = self.USB_RAM_BLOCK
            self.FLASH_WRITE_SIZE = self.USB_RAM_BLOCK


ESP32S3ROM.STUB_CLASS = ESP32S3StubLoader


class ESP32C3StubLoader(ESP32C3ROM):
    """ Access class for ESP32C3 stub loader, runs on top of ROM.

    (Basically the same as ESP32StubLoader, but different base class.
    Can possibly be made into a mixin.)
    """
    FLASH_WRITE_SIZE = 0x4000  # matches MAX_WRITE_BLOCK in stub_loader.c
    STATUS_BYTES_LENGTH = 2  # same as ESP8266, different to ESP32 ROM
    IS_STUB = True

    def __init__(self, rom_loader):
        self.secure_download_mode = rom_loader.secure_download_mode
        self._port = rom_loader._port
        self._trace_enabled = rom_loader._trace_enabled
        self.flush_input()  # resets _slip_reader


ESP32C3ROM.STUB_CLASS = ESP32C3StubLoader


class ESP32H2StubLoader(ESP32H2ROM):
    """ Access class for ESP32H2 stub loader, runs on top of ROM.

    (Basically the same as ESP32StubLoader, but different base class.
    Can possibly be made into a mixin.)
    """
    FLASH_WRITE_SIZE = 0x4000  # matches MAX_WRITE_BLOCK in stub_loader.c
    STATUS_BYTES_LENGTH = 2  # same as ESP8266, different to ESP32 ROM
    IS_STUB = True

    def __init__(self, rom_loader):
        self.secure_download_mode = rom_loader.secure_download_mode
        self._port = rom_loader._port
        self._trace_enabled = rom_loader._trace_enabled
        self.flush_input()  # resets _slip_reader


ESP32H2ROM.STUB_CLASS = ESP32H2StubLoader


class ESP8684StubLoader(ESP8684ROM):
    """ Access class for ESP8684 stub loader, runs on top of ROM.

    (Basically the same as ESP32StubLoader, but different base class.
    Can possibly be made into a mixin.)
    """
    FLASH_WRITE_SIZE = 0x4000  # matches MAX_WRITE_BLOCK in stub_loader.c
    STATUS_BYTES_LENGTH = 2  # same as ESP8266, different to ESP32 ROM
    IS_STUB = True

    def __init__(self, rom_loader):
        self.secure_download_mode = rom_loader.secure_download_mode
        self._port = rom_loader._port
        self._trace_enabled = rom_loader._trace_enabled
        self.flush_input()  # resets _slip_reader


ESP8684ROM.STUB_CLASS = ESP8684StubLoader


class ESPBOOTLOADER(object):
    """ These are constants related to software ESP8266 bootloader, working with 'v2' image files """

    # First byte of the "v2" application image
    IMAGE_V2_MAGIC = 0xea

    # First 'segment' value in a "v2" application image, appears to be a constant version value?
    IMAGE_V2_SEGMENT = 4


def LoadFirmwareImage(chip, filename):
    """ Load a firmware image. Can be for any supported SoC.

        ESP8266 images will be examined to determine if they are original ROM firmware images (ESP8266ROMFirmwareImage)
        or "v2" OTA bootloader images.

        Returns a BaseFirmwareImage subclass, either ESP8266ROMFirmwareImage (v1) or ESP8266V2FirmwareImage (v2).
    """
    chip = chip.lower().replace("-", "")
    with open(filename, 'rb') as f:
        if chip == 'esp32':
            return ESP32FirmwareImage(f)
        elif chip == "esp32s2":
            return ESP32S2FirmwareImage(f)
        elif chip == "esp32s3beta2":
            return ESP32S3BETA2FirmwareImage(f)
        elif chip == "esp32s3":
            return ESP32S3FirmwareImage(f)
        elif chip == 'esp32c3':
            return ESP32C3FirmwareImage(f)
        elif chip == 'esp32c6beta':
            return ESP32C6BETAFirmwareImage(f)
        elif chip == 'esp32h2':
            return ESP32H2FirmwareImage(f)
        elif chip == 'esp8684':
            return ESP8684FirmwareImage(f)
        else:  # Otherwise, ESP8266 so look at magic to determine the image type
            magic = ord(f.read(1))
            f.seek(0)
            if magic == ESPLoader.ESP_IMAGE_MAGIC:
                return ESP8266ROMFirmwareImage(f)
            elif magic == ESPBOOTLOADER.IMAGE_V2_MAGIC:
                return ESP8266V2FirmwareImage(f)
            else:
                raise FatalError("Invalid image magic number: %d" % magic)


class ImageSegment(object):
    """ Wrapper class for a segment in an ESP image
    (very similar to a section in an ELFImage also) """
    def __init__(self, addr, data, file_offs=None):
        self.addr = addr
        self.data = data
        self.file_offs = file_offs
        self.include_in_checksum = True
        if self.addr != 0:
            self.pad_to_alignment(4)  # pad all "real" ImageSegments 4 byte aligned length

    def copy_with_new_addr(self, new_addr):
        """ Return a new ImageSegment with same data, but mapped at
        a new address. """
        return ImageSegment(new_addr, self.data, 0)

    def split_image(self, split_len):
        """ Return a new ImageSegment which splits "split_len" bytes
        from the beginning of the data. Remaining bytes are kept in
        this segment object (and the start address is adjusted to match.) """
        result = copy.copy(self)
        result.data = self.data[:split_len]
        self.data = self.data[split_len:]
        self.addr += split_len
        self.file_offs = None
        result.file_offs = None
        return result

    def __repr__(self):
        r = "len 0x%05x load 0x%08x" % (len(self.data), self.addr)
        if self.file_offs is not None:
            r += " file_offs 0x%08x" % (self.file_offs)
        return r

    def get_memory_type(self, image):
        """
        Return a list describing the memory type(s) that is covered by this
        segment's start address.
        """
        return [map_range[2] for map_range in image.ROM_LOADER.MEMORY_MAP if map_range[0] <= self.addr < map_range[1]]

    def pad_to_alignment(self, alignment):
        self.data = pad_to(self.data, alignment, b'\x00')


class ELFSection(ImageSegment):
    """ Wrapper class for a section in an ELF image, has a section
    name as well as the common properties of an ImageSegment. """
    def __init__(self, name, addr, data):
        super(ELFSection, self).__init__(addr, data)
        self.name = name.decode("utf-8")

    def __repr__(self):
        return "%s %s" % (self.name, super(ELFSection, self).__repr__())


class BaseFirmwareImage(object):
    SEG_HEADER_LEN = 8
    SHA256_DIGEST_LEN = 32

    """ Base class with common firmware image functions """
    def __init__(self):
        self.segments = []
        self.entrypoint = 0
        self.elf_sha256 = None
        self.elf_sha256_offset = 0

    def load_common_header(self, load_file, expected_magic):
        (magic, segments, self.flash_mode, self.flash_size_freq, self.entrypoint) = struct.unpack('<BBBBI', load_file.read(8))

        if magic != expected_magic:
            raise FatalError('Invalid firmware image magic=0x%x' % (magic))
        return segments

    def verify(self):
        if len(self.segments) > 16:
            raise FatalError('Invalid segment count %d (max 16). Usually this indicates a linker script problem.' % len(self.segments))

    def load_segment(self, f, is_irom_segment=False):
        """ Load the next segment from the image file """
        file_offs = f.tell()
        (offset, size) = struct.unpack('<II', f.read(8))
        self.warn_if_unusual_segment(offset, size, is_irom_segment)
        segment_data = f.read(size)
        if len(segment_data) < size:
            raise FatalError('End of file reading segment 0x%x, length %d (actual length %d)' % (offset, size, len(segment_data)))
        segment = ImageSegment(offset, segment_data, file_offs)
        self.segments.append(segment)
        return segment

    def warn_if_unusual_segment(self, offset, size, is_irom_segment):
        if not is_irom_segment:
            if offset > 0x40200000 or offset < 0x3ffe0000 or size > 65536:
                print('WARNING: Suspicious segment 0x%x, length %d' % (offset, size))

    def maybe_patch_segment_data(self, f, segment_data):
        """If SHA256 digest of the ELF file needs to be inserted into this segment, do so. Returns segment data."""
        segment_len = len(segment_data)
        file_pos = f.tell()  # file_pos is position in the .bin file
        if self.elf_sha256_offset >= file_pos and self.elf_sha256_offset < file_pos + segment_len:
            # SHA256 digest needs to be patched into this binary segment,
            # calculate offset of the digest inside the binary segment.
            patch_offset = self.elf_sha256_offset - file_pos
            # Sanity checks
            if patch_offset < self.SEG_HEADER_LEN or patch_offset + self.SHA256_DIGEST_LEN > segment_len:
                raise FatalError('Cannot place SHA256 digest on segment boundary'
                                 '(elf_sha256_offset=%d, file_pos=%d, segment_size=%d)' %
                                 (self.elf_sha256_offset, file_pos, segment_len))
            # offset relative to the data part
            patch_offset -= self.SEG_HEADER_LEN
            if segment_data[patch_offset:patch_offset + self.SHA256_DIGEST_LEN] != b'\x00' * self.SHA256_DIGEST_LEN:
                raise FatalError('Contents of segment at SHA256 digest offset 0x%x are not all zero. Refusing to overwrite.' %
                                 self.elf_sha256_offset)
            assert(len(self.elf_sha256) == self.SHA256_DIGEST_LEN)
            segment_data = segment_data[0:patch_offset] + self.elf_sha256 + \
                segment_data[patch_offset + self.SHA256_DIGEST_LEN:]
        return segment_data

    def save_segment(self, f, segment, checksum=None):
        """ Save the next segment to the image file, return next checksum value if provided """
        segment_data = self.maybe_patch_segment_data(f, segment.data)
        f.write(struct.pack('<II', segment.addr, len(segment_data)))
        f.write(segment_data)
        if checksum is not None:
            return ESPLoader.checksum(segment_data, checksum)

    def read_checksum(self, f):
        """ Return ESPLoader checksum from end of just-read image """
        # Skip the padding. The checksum is stored in the last byte so that the
        # file is a multiple of 16 bytes.
        align_file_position(f, 16)
        return ord(f.read(1))

    def calculate_checksum(self):
        """ Calculate checksum of loaded image, based on segments in
        segment array.
        """
        checksum = ESPLoader.ESP_CHECKSUM_MAGIC
        for seg in self.segments:
            if seg.include_in_checksum:
                checksum = ESPLoader.checksum(seg.data, checksum)
        return checksum

    def append_checksum(self, f, checksum):
        """ Append ESPLoader checksum to the just-written image """
        align_file_position(f, 16)
        f.write(struct.pack(b'B', checksum))

    def write_common_header(self, f, segments):
        f.write(struct.pack('<BBBBI', ESPLoader.ESP_IMAGE_MAGIC, len(segments),
                            self.flash_mode, self.flash_size_freq, self.entrypoint))

    def is_irom_addr(self, addr):
        """ Returns True if an address starts in the irom region.
        Valid for ESP8266 only.
        """
        return ESP8266ROM.IROM_MAP_START <= addr < ESP8266ROM.IROM_MAP_END

    def get_irom_segment(self):
        irom_segments = [s for s in self.segments if self.is_irom_addr(s.addr)]
        if len(irom_segments) > 0:
            if len(irom_segments) != 1:
                raise FatalError('Found %d segments that could be irom0. Bad ELF file?' % len(irom_segments))
            return irom_segments[0]
        return None

    def get_non_irom_segments(self):
        irom_segment = self.get_irom_segment()
        return [s for s in self.segments if s != irom_segment]

    def merge_adjacent_segments(self):
        if not self.segments:
            return  # nothing to merge

        segments = []
        # The easiest way to merge the sections is the browse them backward.
        for i in range(len(self.segments) - 1, 0, -1):
            # elem is the previous section, the one `next_elem` may need to be
            # merged in
            elem = self.segments[i - 1]
            next_elem = self.segments[i]
            if all((elem.get_memory_type(self) == next_elem.get_memory_type(self),
                    elem.include_in_checksum == next_elem.include_in_checksum,
                    next_elem.addr == elem.addr + len(elem.data))):
                # Merge any segment that ends where the next one starts, without spanning memory types
                #
                # (don't 'pad' any gaps here as they may be excluded from the image due to 'noinit'
                # or other reasons.)
                elem.data += next_elem.data
            else:
                # The section next_elem cannot be merged into the previous one,
                # which means it needs to be part of the final segments.
                # As we are browsing the list backward, the elements need to be
                # inserted at the beginning of the final list.
                segments.insert(0, next_elem)

        # The first segment will always be here as it cannot be merged into any
        # "previous" section.
        segments.insert(0, self.segments[0])

        # note: we could sort segments here as well, but the ordering of segments is sometimes
        # important for other reasons (like embedded ELF SHA-256), so we assume that the linker
        # script will have produced any adjacent sections in linear order in the ELF, anyhow.
        self.segments = segments


class ESP8266ROMFirmwareImage(BaseFirmwareImage):
    """ 'Version 1' firmware image, segments loaded directly by the ROM bootloader. """

    ROM_LOADER = ESP8266ROM

    def __init__(self, load_file=None):
        super(ESP8266ROMFirmwareImage, self).__init__()
        self.flash_mode = 0
        self.flash_size_freq = 0
        self.version = 1

        if load_file is not None:
            segments = self.load_common_header(load_file, ESPLoader.ESP_IMAGE_MAGIC)

            for _ in range(segments):
                self.load_segment(load_file)
            self.checksum = self.read_checksum(load_file)

            self.verify()

    def default_output_name(self, input_file):
        """ Derive a default output name from the ELF name. """
        return input_file + '-'

    def save(self, basename):
        """ Save a set of V1 images for flashing. Parameter is a base filename. """
        # IROM data goes in its own plain binary file
        irom_segment = self.get_irom_segment()
        if irom_segment is not None:
            with open("%s0x%05x.bin" % (basename, irom_segment.addr - ESP8266ROM.IROM_MAP_START), "wb") as f:
                f.write(irom_segment.data)

        # everything but IROM goes at 0x00000 in an image file
        normal_segments = self.get_non_irom_segments()
        with open("%s0x00000.bin" % basename, 'wb') as f:
            self.write_common_header(f, normal_segments)
            checksum = ESPLoader.ESP_CHECKSUM_MAGIC
            for segment in normal_segments:
                checksum = self.save_segment(f, segment, checksum)
            self.append_checksum(f, checksum)


ESP8266ROM.BOOTLOADER_IMAGE = ESP8266ROMFirmwareImage


class ESP8266V2FirmwareImage(BaseFirmwareImage):
    """ 'Version 2' firmware image, segments loaded by software bootloader stub
        (ie Espressif bootloader or rboot)
    """

    ROM_LOADER = ESP8266ROM

    def __init__(self, load_file=None):
        super(ESP8266V2FirmwareImage, self).__init__()
        self.version = 2
        if load_file is not None:
            segments = self.load_common_header(load_file, ESPBOOTLOADER.IMAGE_V2_MAGIC)
            if segments != ESPBOOTLOADER.IMAGE_V2_SEGMENT:
                # segment count is not really segment count here, but we expect to see '4'
                print('Warning: V2 header has unexpected "segment" count %d (usually 4)' % segments)

            # irom segment comes before the second header
            #
            # the file is saved in the image with a zero load address
            # in the header, so we need to calculate a load address
            irom_segment = self.load_segment(load_file, True)
            irom_segment.addr = 0  # for actual mapped addr, add ESP8266ROM.IROM_MAP_START + flashing_addr + 8
            irom_segment.include_in_checksum = False

            first_flash_mode = self.flash_mode
            first_flash_size_freq = self.flash_size_freq
            first_entrypoint = self.entrypoint
            # load the second header

            segments = self.load_common_header(load_file, ESPLoader.ESP_IMAGE_MAGIC)

            if first_flash_mode != self.flash_mode:
                print('WARNING: Flash mode value in first header (0x%02x) disagrees with second (0x%02x). Using second value.'
                      % (first_flash_mode, self.flash_mode))
            if first_flash_size_freq != self.flash_size_freq:
                print('WARNING: Flash size/freq value in first header (0x%02x) disagrees with second (0x%02x). Using second value.'
                      % (first_flash_size_freq, self.flash_size_freq))
            if first_entrypoint != self.entrypoint:
                print('WARNING: Entrypoint address in first header (0x%08x) disagrees with second header (0x%08x). Using second value.'
                      % (first_entrypoint, self.entrypoint))

            # load all the usual segments
            for _ in range(segments):
                self.load_segment(load_file)
            self.checksum = self.read_checksum(load_file)

            self.verify()

    def default_output_name(self, input_file):
        """ Derive a default output name from the ELF name. """
        irom_segment = self.get_irom_segment()
        if irom_segment is not None:
            irom_offs = irom_segment.addr - ESP8266ROM.IROM_MAP_START
        else:
            irom_offs = 0
        return "%s-0x%05x.bin" % (os.path.splitext(input_file)[0],
                                  irom_offs & ~(ESPLoader.FLASH_SECTOR_SIZE - 1))

    def save(self, filename):
        with open(filename, 'wb') as f:
            # Save first header for irom0 segment
            f.write(struct.pack(b'<BBBBI', ESPBOOTLOADER.IMAGE_V2_MAGIC, ESPBOOTLOADER.IMAGE_V2_SEGMENT,
                                self.flash_mode, self.flash_size_freq, self.entrypoint))

            irom_segment = self.get_irom_segment()
            if irom_segment is not None:
                # save irom0 segment, make sure it has load addr 0 in the file
                irom_segment = irom_segment.copy_with_new_addr(0)
                irom_segment.pad_to_alignment(16)  # irom_segment must end on a 16 byte boundary
                self.save_segment(f, irom_segment)

            # second header, matches V1 header and contains loadable segments
            normal_segments = self.get_non_irom_segments()
            self.write_common_header(f, normal_segments)
            checksum = ESPLoader.ESP_CHECKSUM_MAGIC
            for segment in normal_segments:
                checksum = self.save_segment(f, segment, checksum)
            self.append_checksum(f, checksum)

        # calculate a crc32 of entire file and append
        # (algorithm used by recent 8266 SDK bootloaders)
        with open(filename, 'rb') as f:
            crc = esp8266_crc32(f.read())
        with open(filename, 'ab') as f:
            f.write(struct.pack(b'<I', crc))


def esp8266_crc32(data):
    """
    CRC32 algorithm used by 8266 SDK bootloader (and gen_appbin.py).
    """
    crc = binascii.crc32(data, 0) & 0xFFFFFFFF
    if crc & 0x80000000:
        return crc ^ 0xFFFFFFFF
    else:
        return crc + 1
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
